antmicro/ddr5-tester/assets/previews/layer0.webp

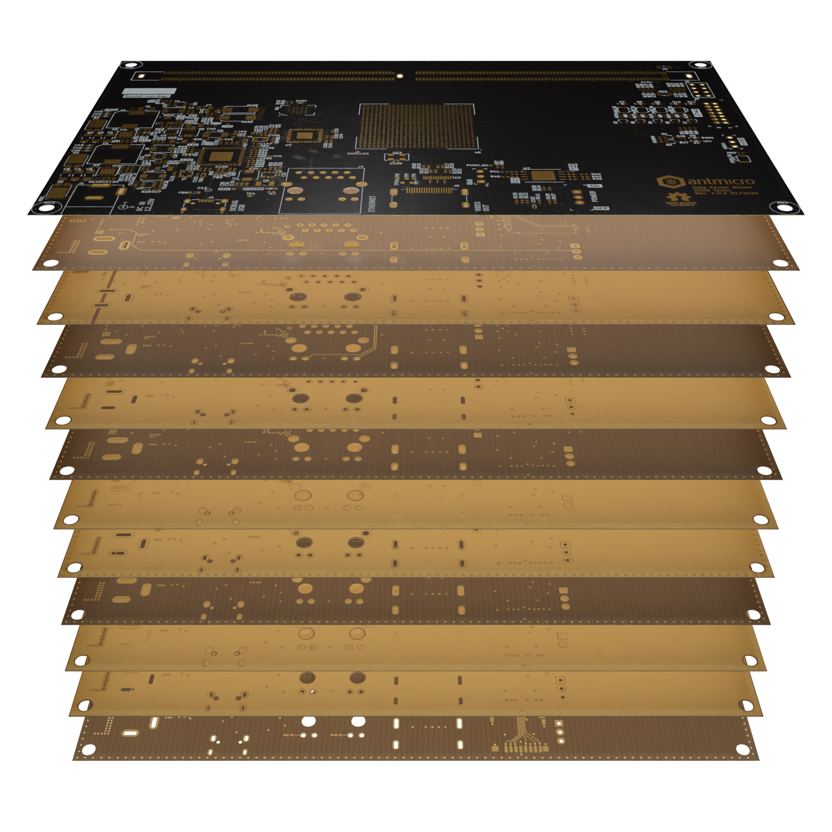
assets/previews/layer0.webp
