antmicro/ddr5-tester/assets/previews/layer2.png

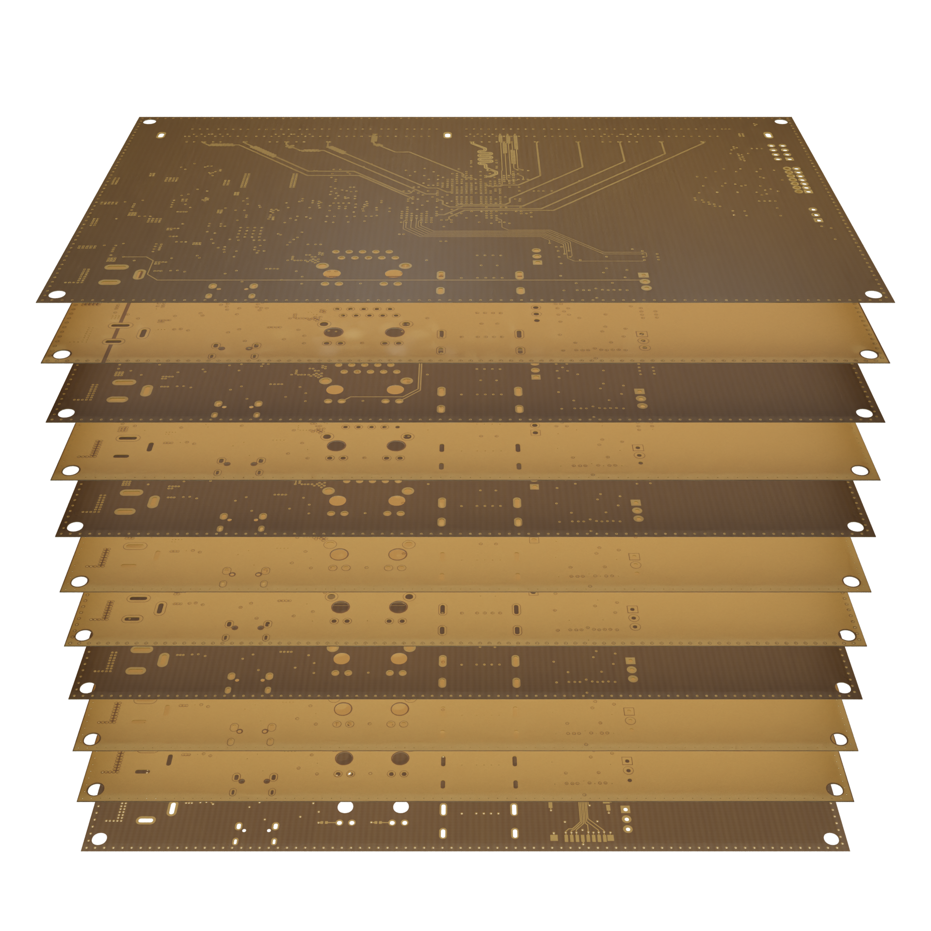
assets/previews/layer2.png
