antmicro/ddr5-tester/assets/previews/layer3.png

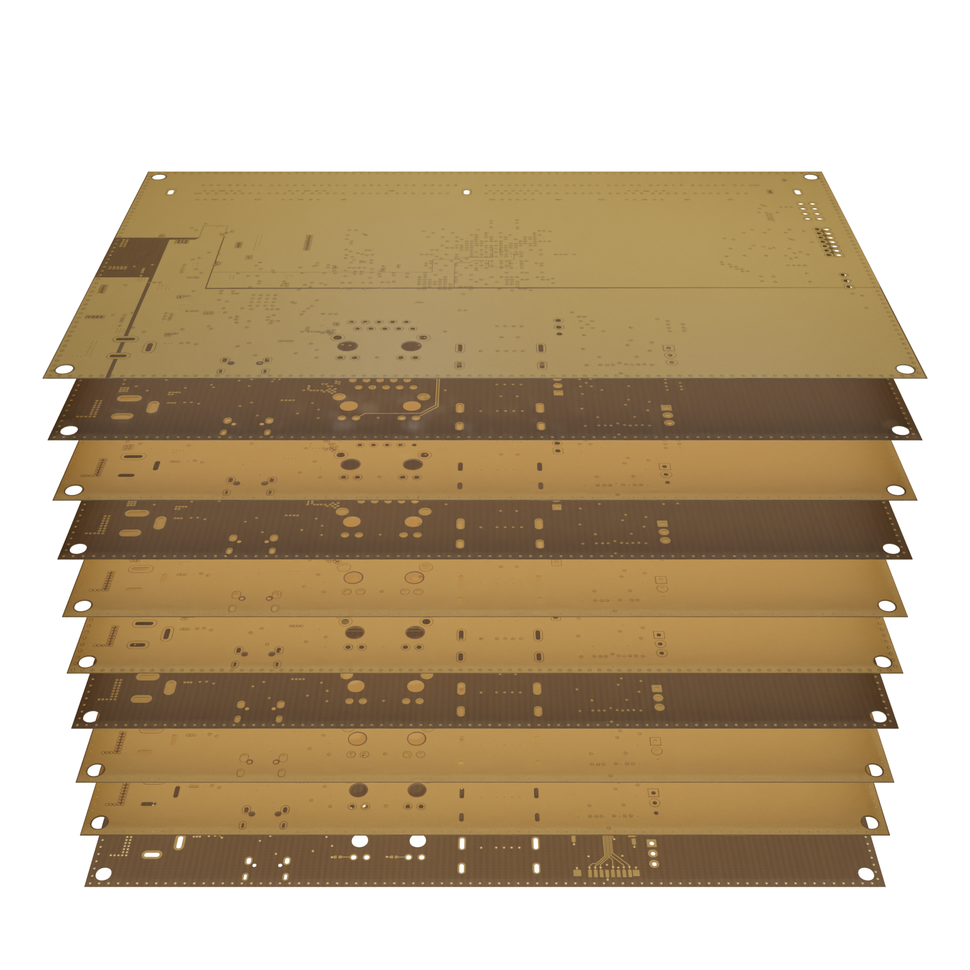
assets/previews/layer3.png
