antmicro/ddr5-tester/assets/previews/layer4.png

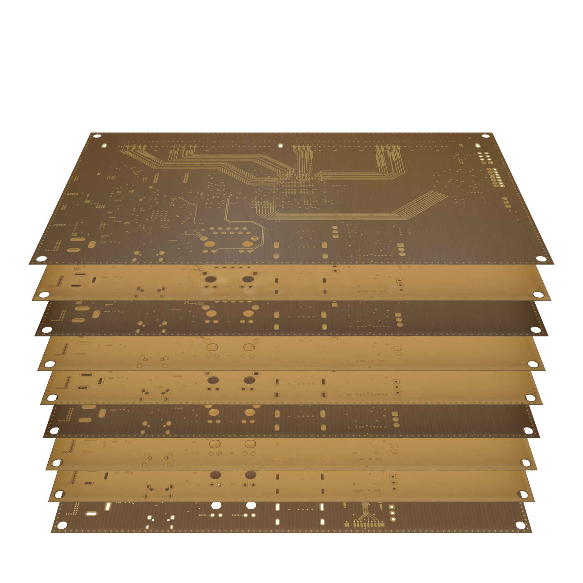
assets/previews/layer4.png
