antmicro/ddr5-tester/assets/previews/layer5.png

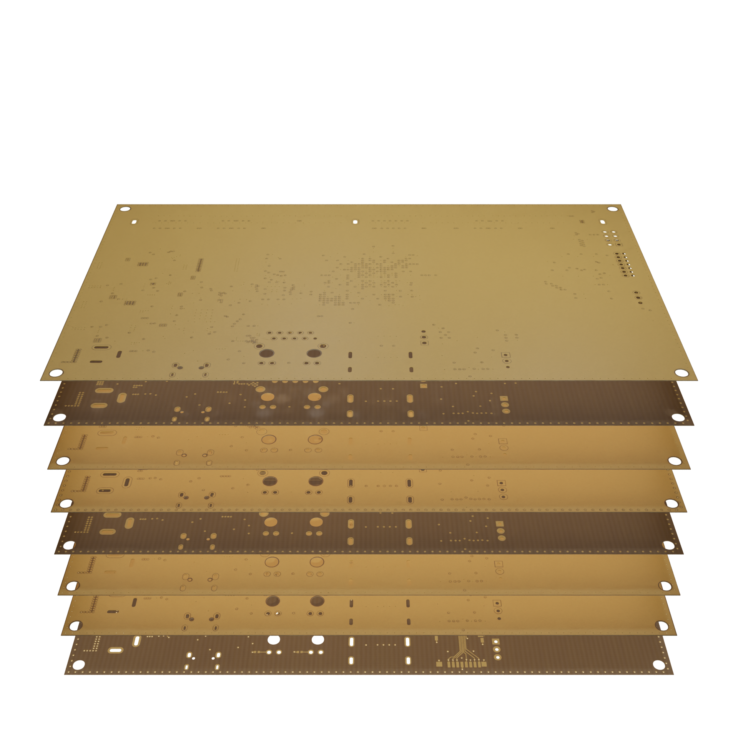
assets/previews/layer5.png
