antmicro/ddr5-tester/assets/previews/layer7.png

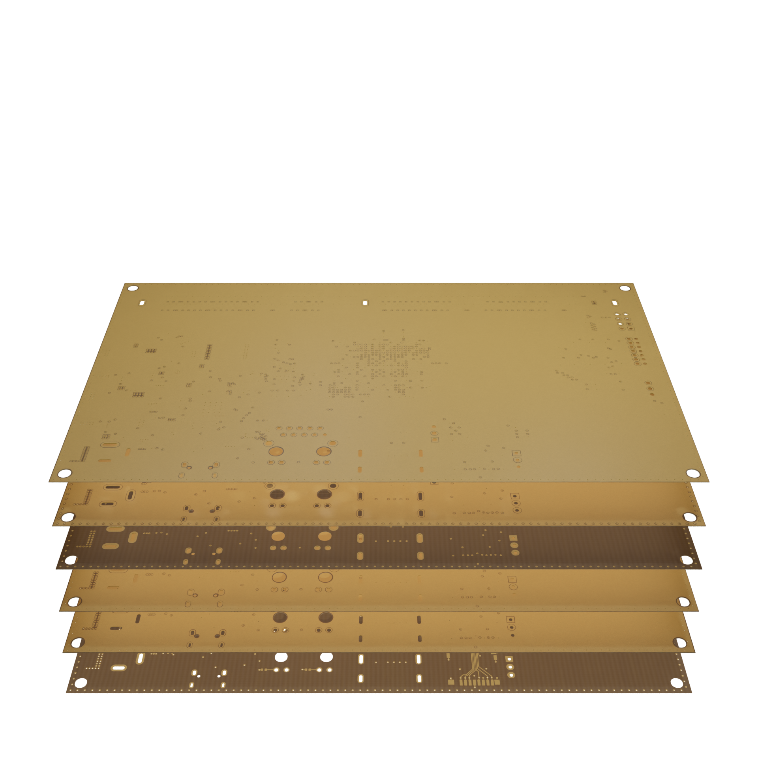
assets/previews/layer7.png
