antmicro/ddr5-tester/assets/previews/layer7_thumbnail.png

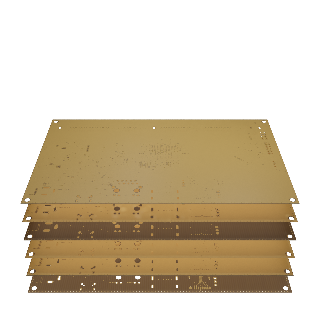
assets/previews/layer7_thumbnail.png
