antmicro/ddr5-tester/assets/previews/layer8.png

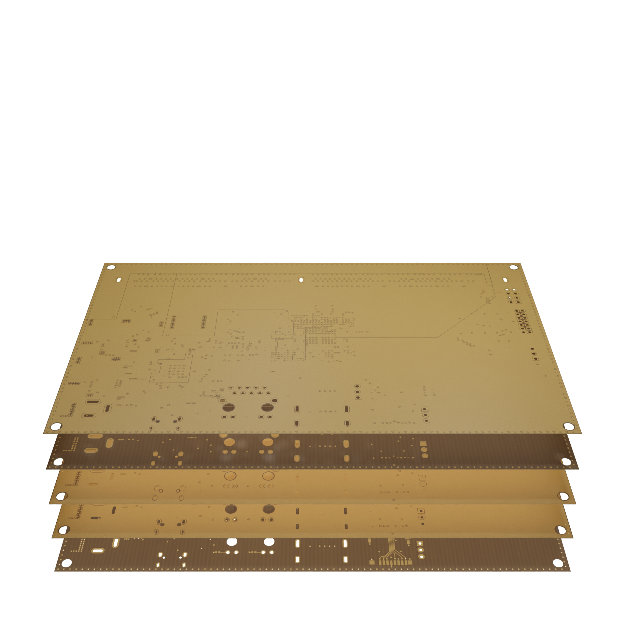
assets/previews/layer8.png
