antmicro/ddr5-tester/assets/previews/layer9.png

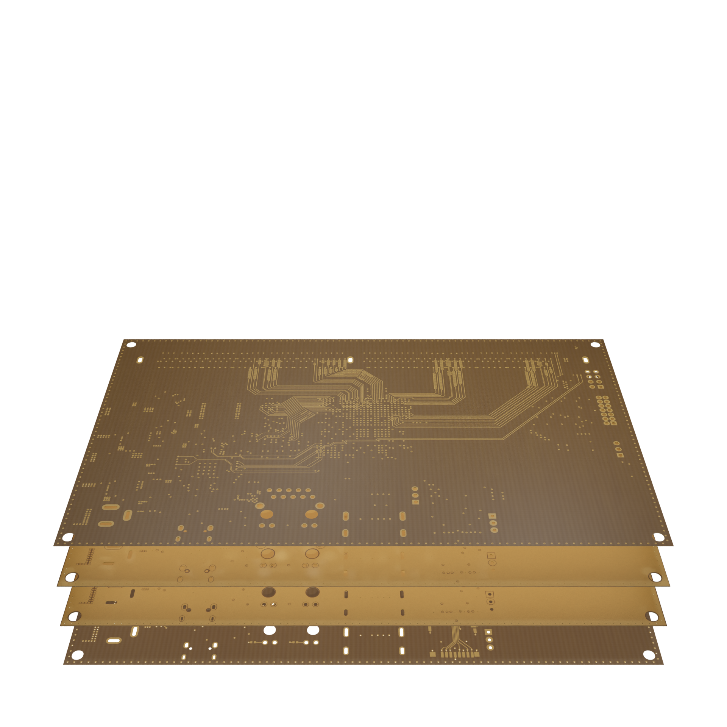
assets/previews/layer9.png
