antmicro/ddr5-tester/assets/previews/layer10.png

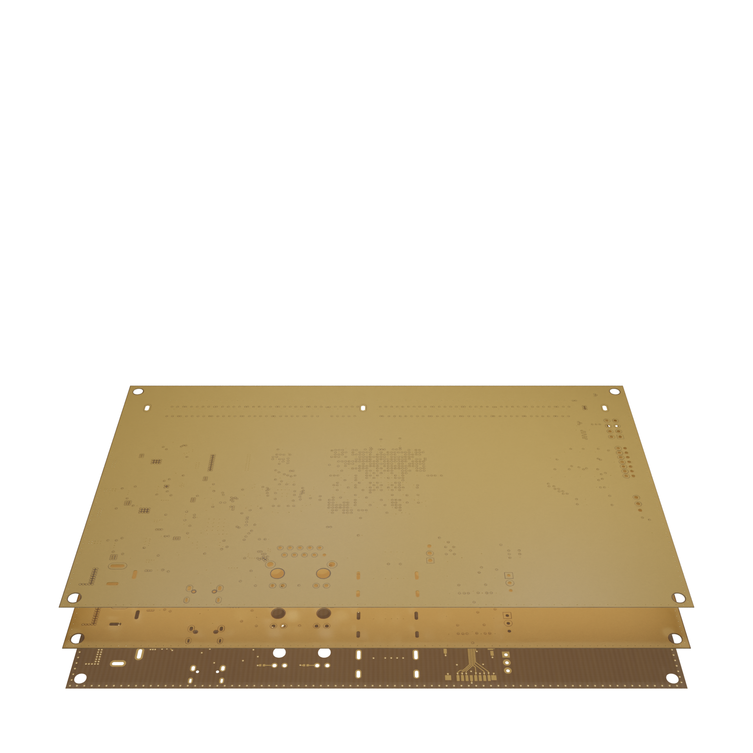
assets/previews/layer10.png
