antmicro/ddr5-tester/assets/previews/layer10_thumbnail.png

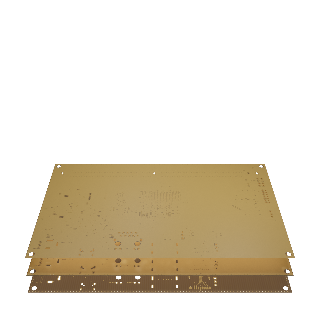
assets/previews/layer10_thumbnail.png
