antmicro/ddr5-tester/assets/previews/layer11.png

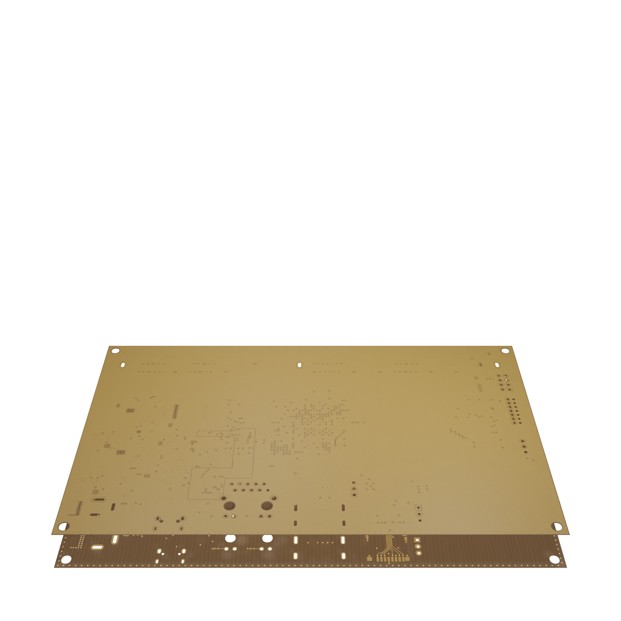
assets/previews/layer11.png
