antmicro/ddr5-tester/assets/previews/layer12.png

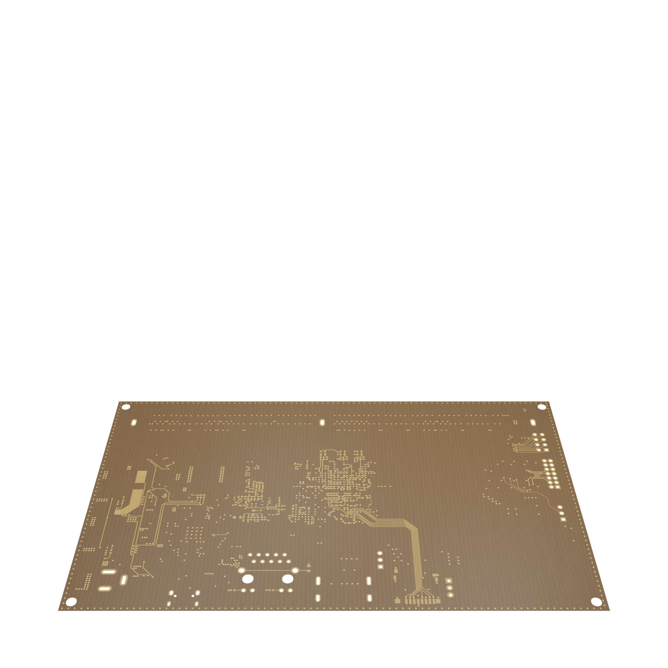
assets/previews/layer12.png
