antmicro/ddr5-tester/assets/previews/leftB.png

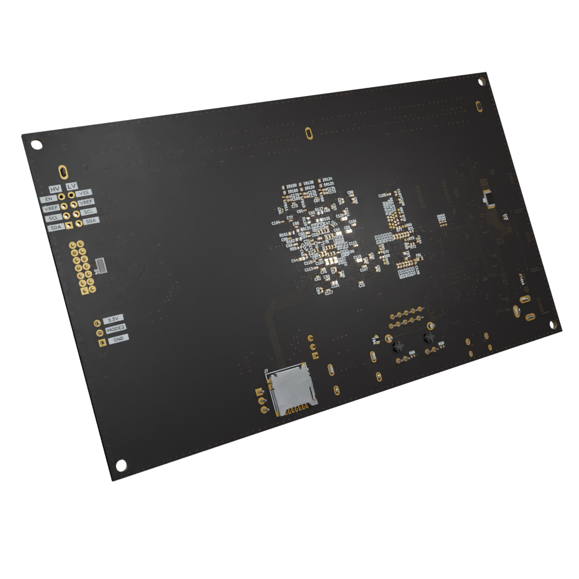
assets/previews/leftB.png
