antmicro/ddr5-tester/assets/previews/leftT.png

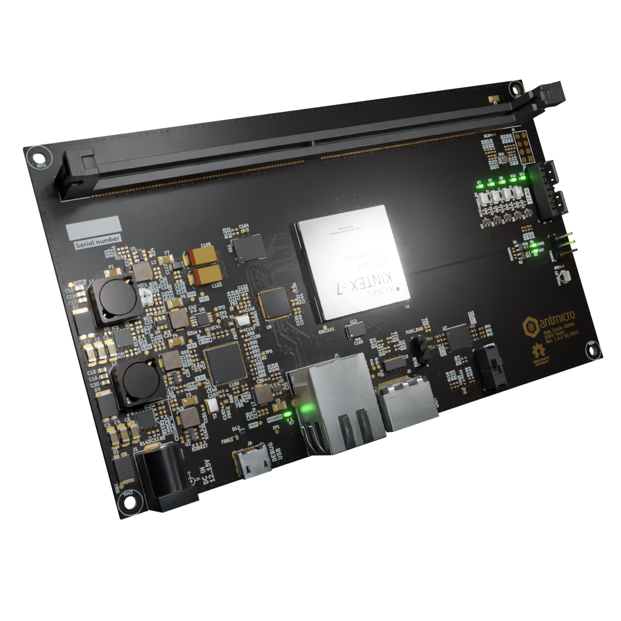
assets/previews/leftT.png
