antmicro/ddr5-tester/assets/previews/orthoB.png

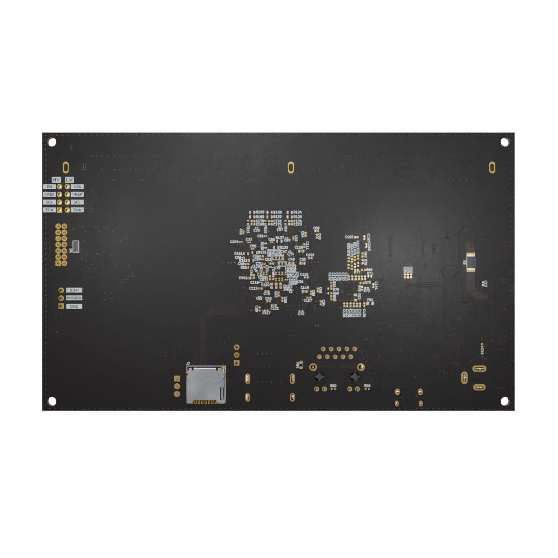
assets/previews/orthoB.png
