antmicro/ddr5-tester/assets/previews/orthoT.png

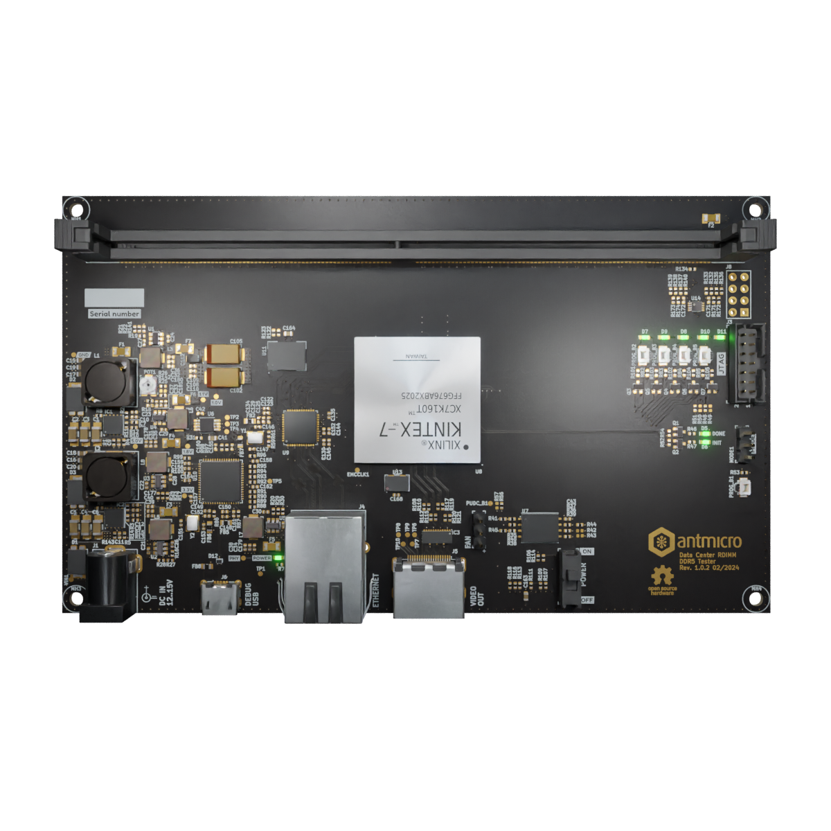
assets/previews/orthoT.png
