antmicro/ddr5-tester/assets/previews/photoB.png

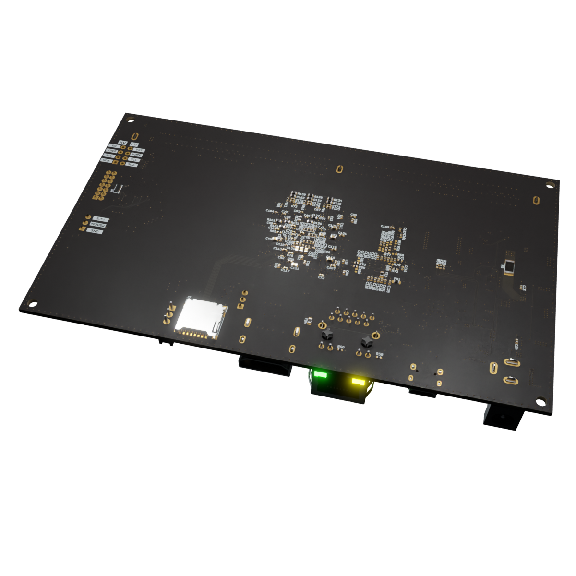
assets/previews/photoB.png
