antmicro/ddr5-tester/assets/previews/photoT.png

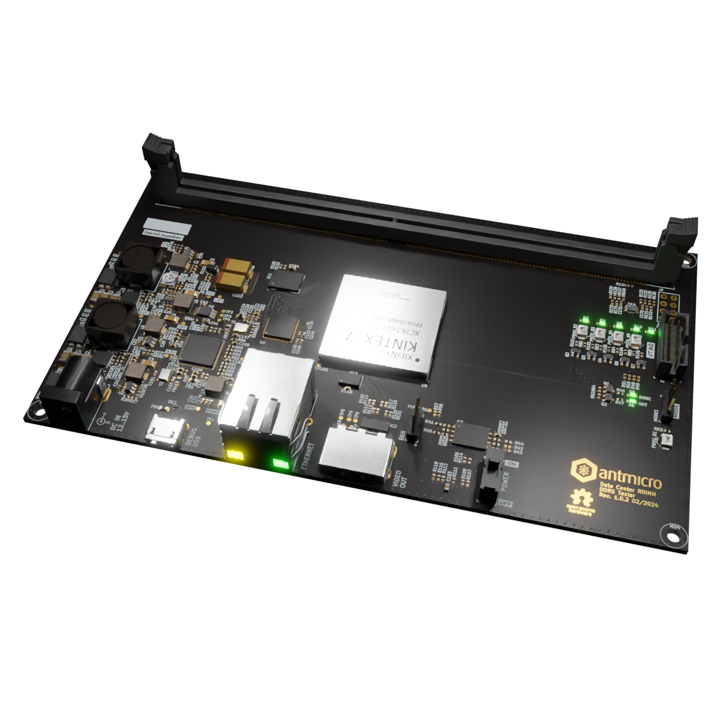
assets/previews/photoT.png
