antmicro/ddr5-tester/assets/previews/rightB.png

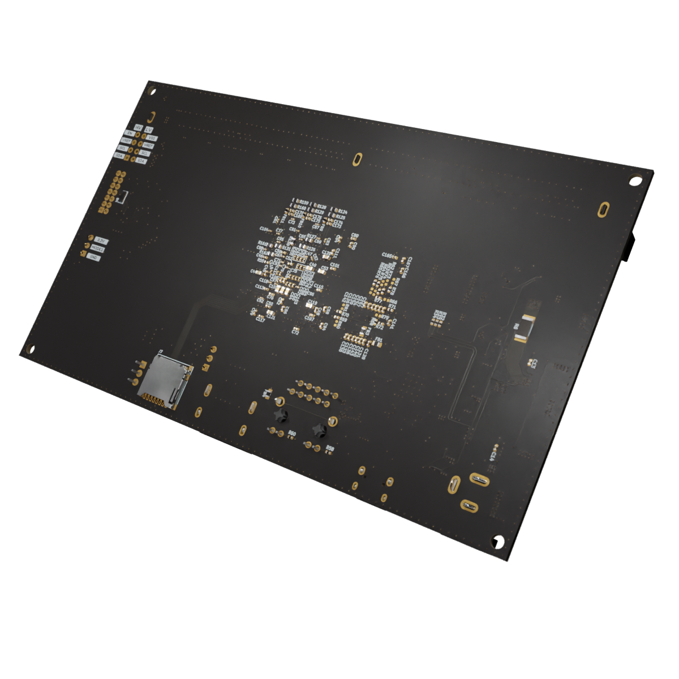
assets/previews/rightB.png
