antmicro/ddr5-tester/assets/previews/rightT.png

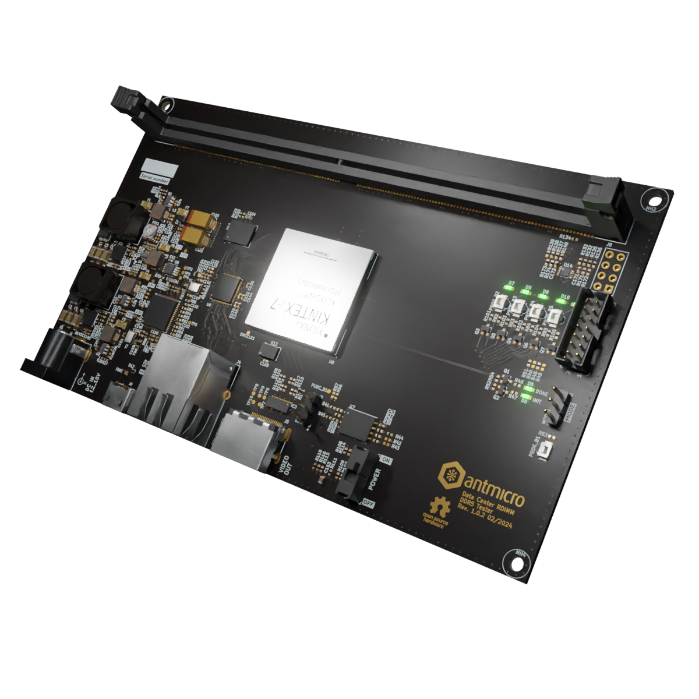
assets/previews/rightT.png
