antmicro/ddr5-tester/DDR5.kicad_sch

## KiCad design DDR5.kicad_sch (2024-02-20)

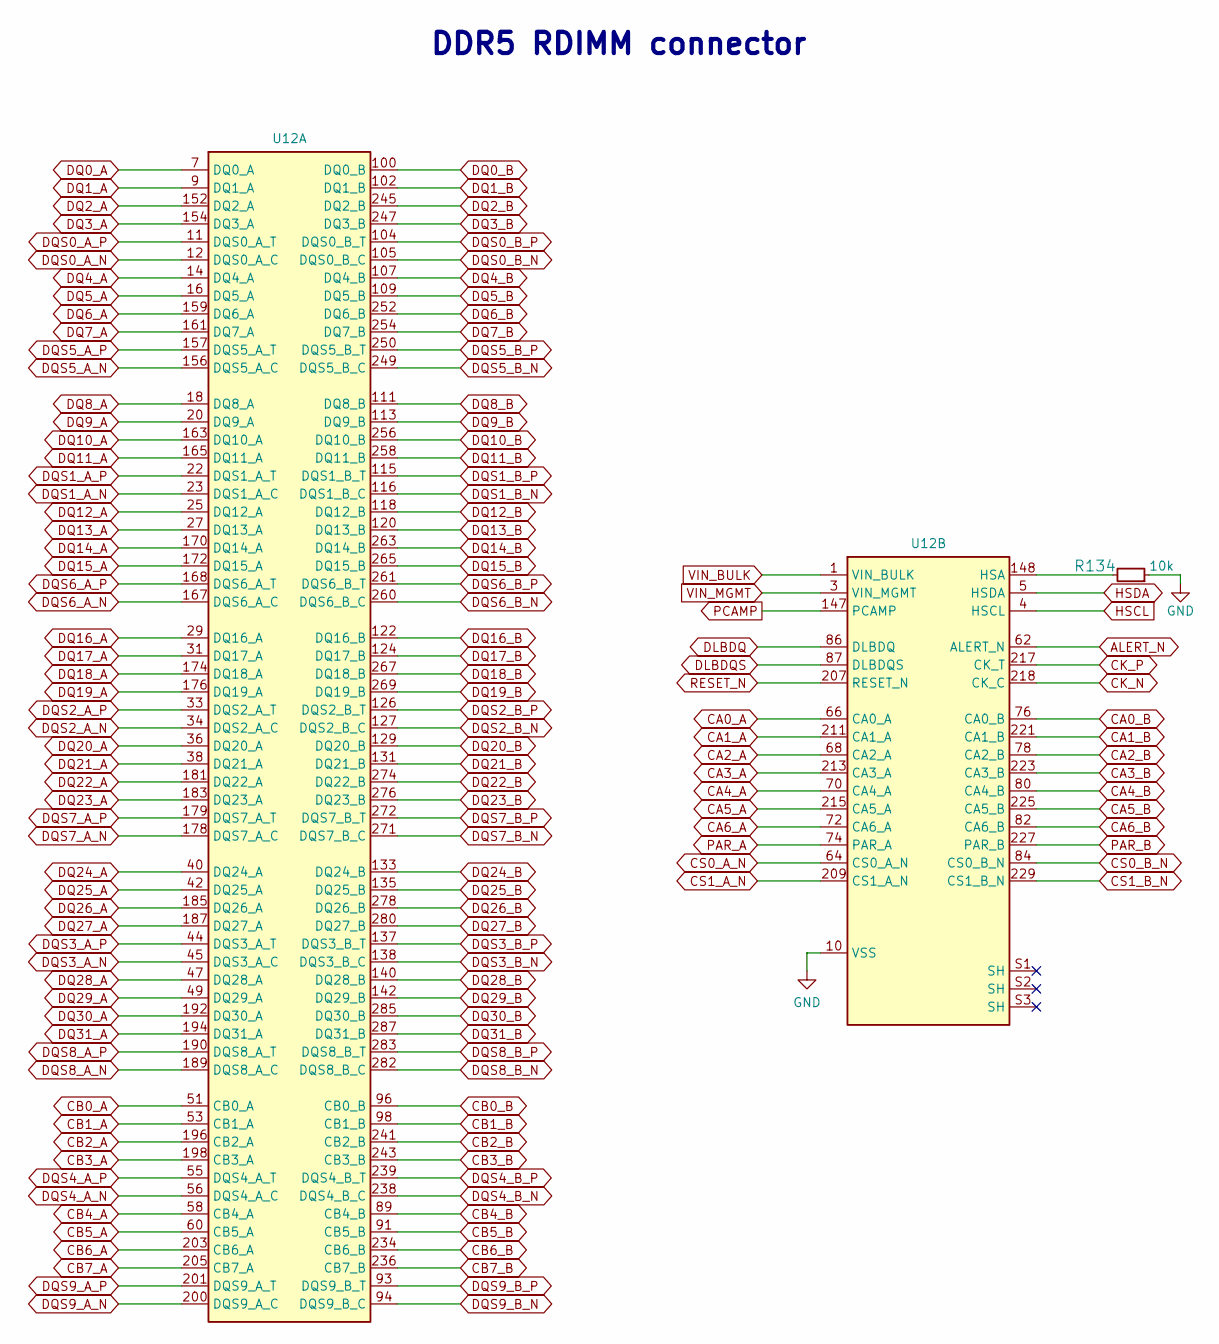
[picture p35: schematic DDR5.kicad_sch]

Parts:
R134: R_10k_0402; R_0402_1005Metric; Tolerance 1%; MPN CR0402-FX-1002GLF
U12: Bus_DDR5_DDR504111002KQ; Bus_DDR5_Socket_Amphenol_DDR504111002KQ; MPN DDR504111002KQ

Connections:
ALERT_N: U12.62 (ALERT_N)
CA0_A: U12.66 (CA0_A)
CA0_B: U12.76 (CA0_B)
CA1_A: U12.211 (CA1_A)
CA1_B: U12.221 (CA1_B)
CA2_A: U12.68 (CA2_A)
CA2_B: U12.78 (CA2_B)
CA3_A: U12.213 (CA3_A)
CA3_B: U12.223 (CA3_B)
CA4_A: U12.70 (CA4_A)
CA4_B: U12.80 (CA4_B)
CA5_A: U12.215 (CA5_A)
CA5_B: U12.225 (CA5_B)
CA6_A: U12.72 (CA6_A)
CA6_B: U12.82 (CA6_B)
CB0_A: U12.51 (CB0_A)
CB0_B: U12.96 (CB0_B)
CB1_A: U12.53 (CB1_A)
CB1_B: U12.98 (CB1_B)
CB2_A: U12.196 (CB2_A)
CB2_B: U12.241 (CB2_B)
CB3_A: U12.198 (CB3_A)
CB3_B: U12.243 (CB3_B)
CB4_A: U12.58 (CB4_A)
CB4_B: U12.89 (CB4_B)
CB5_A: U12.60 (CB5_A)
CB5_B: U12.91 (CB5_B)
CB6_A: U12.203 (CB6_A)
CB6_B: U12.234 (CB6_B)
CB7_A: U12.205 (CB7_A)
CB7_B: U12.236 (CB7_B)
CK_N: U12.218 (CK_C)
CK_P: U12.217 (CK_T)
CS0_A_N: U12.64 (CS0_A_N)
CS0_B_N: U12.84 (CS0_B_N)
CS1_A_N: U12.209 (CS1_A_N)
CS1_B_N: U12.229 (CS1_B_N)
DLBDQ: U12.86 (DLBDQ)
DLBDQS: U12.87 (DLBDQS)
DQ0_A: U12.7 (DQ0_A)
DQ0_B: U12.100 (DQ0_B)
DQ1_A: U12.9 (DQ1_A)
DQ1_B: U12.102 (DQ1_B)
DQ2_A: U12.152 (DQ2_A)
DQ2_B: U12.245 (DQ2_B)
DQ3_A: U12.154 (DQ3_A)
DQ3_B: U12.247 (DQ3_B)
DQ4_A: U12.14 (DQ4_A)
DQ4_B: U12.107 (DQ4_B)
DQ5_A: U12.16 (DQ5_A)
DQ5_B: U12.109 (DQ5_B)
DQ6_A: U12.159 (DQ6_A)
DQ6_B: U12.252 (DQ6_B)
DQ7_A: U12.161 (DQ7_A)
DQ7_B: U12.254 (DQ7_B)
DQ8_A: U12.18 (DQ8_A)
DQ8_B: U12.111 (DQ8_B)
DQ9_A: U12.20 (DQ9_A)
DQ9_B: U12.113 (DQ9_B)
DQ10_A: U12.163 (DQ10_A)
DQ10_B: U12.256 (DQ10_B)
DQ11_A: U12.165 (DQ11_A)
DQ11_B: U12.258 (DQ11_B)
DQ12_A: U12.25 (DQ12_A)
DQ12_B: U12.118 (DQ12_B)
DQ13_A: U12.27 (DQ13_A)
DQ13_B: U12.120 (DQ13_B)
DQ14_A: U12.170 (DQ14_A)
DQ14_B: U12.263 (DQ14_B)
DQ15_A: U12.172 (DQ15_A)
DQ15_B: U12.265 (DQ15_B)
DQ16_A: U12.29 (DQ16_A)
DQ16_B: U12.122 (DQ16_B)
DQ17_A: U12.31 (DQ17_A)
DQ17_B: U12.124 (DQ17_B)
DQ18_A: U12.174 (DQ18_A)
DQ18_B: U12.267 (DQ18_B)
DQ19_A: U12.176 (DQ19_A)
DQ19_B: U12.269 (DQ19_B)
DQ20_A: U12.36 (DQ20_A)
DQ20_B: U12.129 (DQ20_B)
DQ21_A: U12.38 (DQ21_A)
DQ21_B: U12.131 (DQ21_B)
DQ22_A: U12.181 (DQ22_A)
DQ22_B: U12.274 (DQ22_B)
DQ23_A: U12.183 (DQ23_A)
DQ23_B: U12.276 (DQ23_B)
DQ24_A: U12.40 (DQ24_A)
DQ24_B: U12.133 (DQ24_B)
DQ25_A: U12.42 (DQ25_A)
DQ25_B: U12.135 (DQ25_B)
DQ26_A: U12.185 (DQ26_A)
DQ26_B: U12.278 (DQ26_B)
DQ27_A: U12.187 (DQ27_A)
DQ27_B: U12.280 (DQ27_B)
DQ28_A: U12.47 (DQ28_A)
DQ28_B: U12.140 (DQ28_B)
DQ29_A: U12.49 (DQ29_A)
DQ29_B: U12.142 (DQ29_B)
DQ30_A: U12.192 (DQ30_A)
DQ30_B: U12.285 (DQ30_B)
DQ31_A: U12.194 (DQ31_A)
DQ31_B: U12.287 (DQ31_B)
DQS0_A_N: U12.12 (DQS0_A_C)
DQS0_A_P: U12.11 (DQS0_A_T)
DQS0_B_N: U12.105 (DQS0_B_C)
DQS0_B_P: U12.104 (DQS0_B_T)
DQS1_A_N: U12.23 (DQS1_A_C)
DQS1_A_P: U12.22 (DQS1_A_T)
DQS1_B_N: U12.116 (DQS1_B_C)
DQS1_B_P: U12.115 (DQS1_B_T)
DQS2_A_N: U12.34 (DQS2_A_C)
DQS2_A_P: U12.33 (DQS2_A_T)
DQS2_B_N: U12.127 (DQS2_B_C)
DQS2_B_P: U12.126 (DQS2_B_T)
DQS3_A_N: U12.45 (DQS3_A_C)
DQS3_A_P: U12.44 (DQS3_A_T)
DQS3_B_N: U12.138 (DQS3_B_C)
DQS3_B_P: U12.137 (DQS3_B_T)
DQS4_A_N: U12.56 (DQS4_A_C)
DQS4_A_P: U12.55 (DQS4_A_T)
DQS4_B_N: U12.238 (DQS4_B_C)
DQS4_B_P: U12.239 (DQS4_B_T)
DQS5_A_N: U12.156 (DQS5_A_C)
DQS5_A_P: U12.157 (DQS5_A_T)
DQS5_B_N: U12.249 (DQS5_B_C)
DQS5_B_P: U12.250 (DQS5_B_T)
DQS6_A_N: U12.167 (DQS6_A_C)
DQS6_A_P: U12.168 (DQS6_A_T)
DQS6_B_N: U12.260 (DQS6_B_C)
DQS6_B_P: U12.261 (DQS6_B_T)
DQS7_A_N: U12.178 (DQS7_A_C)
DQS7_A_P: U12.179 (DQS7_A_T)
DQS7_B_N: U12.271 (DQS7_B_C)
DQS7_B_P: U12.272 (DQS7_B_T)
DQS8_A_N: U12.189 (DQS8_A_C)
DQS8_A_P: U12.190 (DQS8_A_T)
DQS8_B_N: U12.282 (DQS8_B_C)
DQS8_B_P: U12.283 (DQS8_B_T)
DQS9_A_N: U12.200 (DQS9_A_C)
DQS9_A_P: U12.201 (DQS9_A_T)
DQS9_B_N: U12.94 (DQS9_B_C)
DQS9_B_P: U12.93 (DQS9_B_T)
GND: R134.1, U12.6 (VSS), U12.8 (VSS), U12.10 (VSS), U12.13 (VSS), U12.15 (VSS), U12.17 (VSS), U12.19 (VSS), U12.21 (VSS), U12.24 (VSS), U12.26 (VSS), U12.28 (VSS), U12.30 (VSS), U12.32 (VSS), U12.35 (VSS), U12.37 (VSS), U12.39 (VSS), U12.41 (VSS), U12.43 (VSS), U12.46 (VSS), U12.48 (VSS), U12.50 (VSS), U12.52 (VSS), U12.54 (VSS), U12.57 (VSS), U12.59 (VSS), U12.61 (VSS), U12.63 (VSS), U12.65 (VSS), U12.67 (VSS), U12.69 (VSS), U12.71 (VSS), U12.73 (VSS), U12.75 (VSS), U12.77 (VSS), U12.79 (VSS), U12.81 (VSS), U12.83 (VSS), U12.85 (VSS), U12.88 (VSS), U12.90 (VSS), U12.92 (VSS), U12.95 (VSS), U12.97 (VSS), U12.99 (VSS), U12.101 (VSS), U12.103 (VSS), U12.106 (VSS), U12.108 (VSS), U12.110 (VSS), U12.112 (VSS), U12.114 (VSS), U12.117 (VSS), U12.119 (VSS), U12.121 (VSS), U12.123 (VSS), U12.125 (VSS), U12.128 (VSS), U12.130 (VSS), U12.132 (VSS), U12.134 (VSS), U12.136 (VSS), U12.139 (VSS), U12.141 (VSS), U12.143 (VSS), U12.151 (VSS), U12.153 (VSS), U12.155 (VSS), U12.158 (VSS), U12.160 (VSS), U12.162 (VSS), U12.164 (VSS), U12.166 (VSS), U12.169 (VSS), U12.171 (VSS), U12.173 (VSS), U12.175 (VSS), U12.177 (VSS), U12.180 (VSS), U12.182 (VSS), U12.184 (VSS), U12.186 (VSS), U12.188 (VSS), U12.191 (VSS), U12.193 (VSS), U12.195 (VSS), U12.197 (VSS), U12.199 (VSS), U12.202 (VSS), U12.204 (VSS), U12.206 (VSS), U12.208 (VSS), U12.210 (VSS), U12.212 (VSS), U12.214 (VSS), U12.216 (VSS), U12.219 (VSS), U12.222 (VSS), U12.224 (VSS), U12.226 (VSS), U12.228 (VSS), U12.230 (VSS), U12.233 (VSS), U12.235 (VSS), U12.237 (VSS), U12.240 (VSS), U12.242 (VSS), U12.244 (VSS), U12.246 (VSS), U12.248 (VSS), U12.251 (VSS), U12.253 (VSS), U12.255 (VSS), U12.257 (VSS), U12.259 (VSS), U12.262 (VSS), U12.264 (VSS), U12.266 (VSS), U12.268 (VSS), U12.270 (VSS), U12.273 (VSS), U12.275 (VSS), U12.277 (VSS), U12.279 (VSS), U12.281 (VSS), U12.284 (VSS), U12.286 (VSS), U12.288 (VSS)
HSCL: U12.4 (HSCL)
HSDA: U12.5 (HSDA)
unnamed: R134.2, U12.148 (HSA)
PAR_A: U12.74 (PAR_A)
PAR_B: U12.227 (PAR_B)
PCAMP: U12.147 (PCAMP)
RESET_N: U12.207 (RESET_N)
VIN_BULK: U12.1 (VIN_BULK), U12.145 (VIN_BULK), U12.146 (VIN_BULK)
VIN_MGMT: U12.3 (VIN_MGMT)

Notes on the sheet:
DDR5 RDIMM connector
