antmicro/ddr5-tester/config-spi.kicad_sch

## KiCad design config-spi.kicad_sch (2024-02-20)

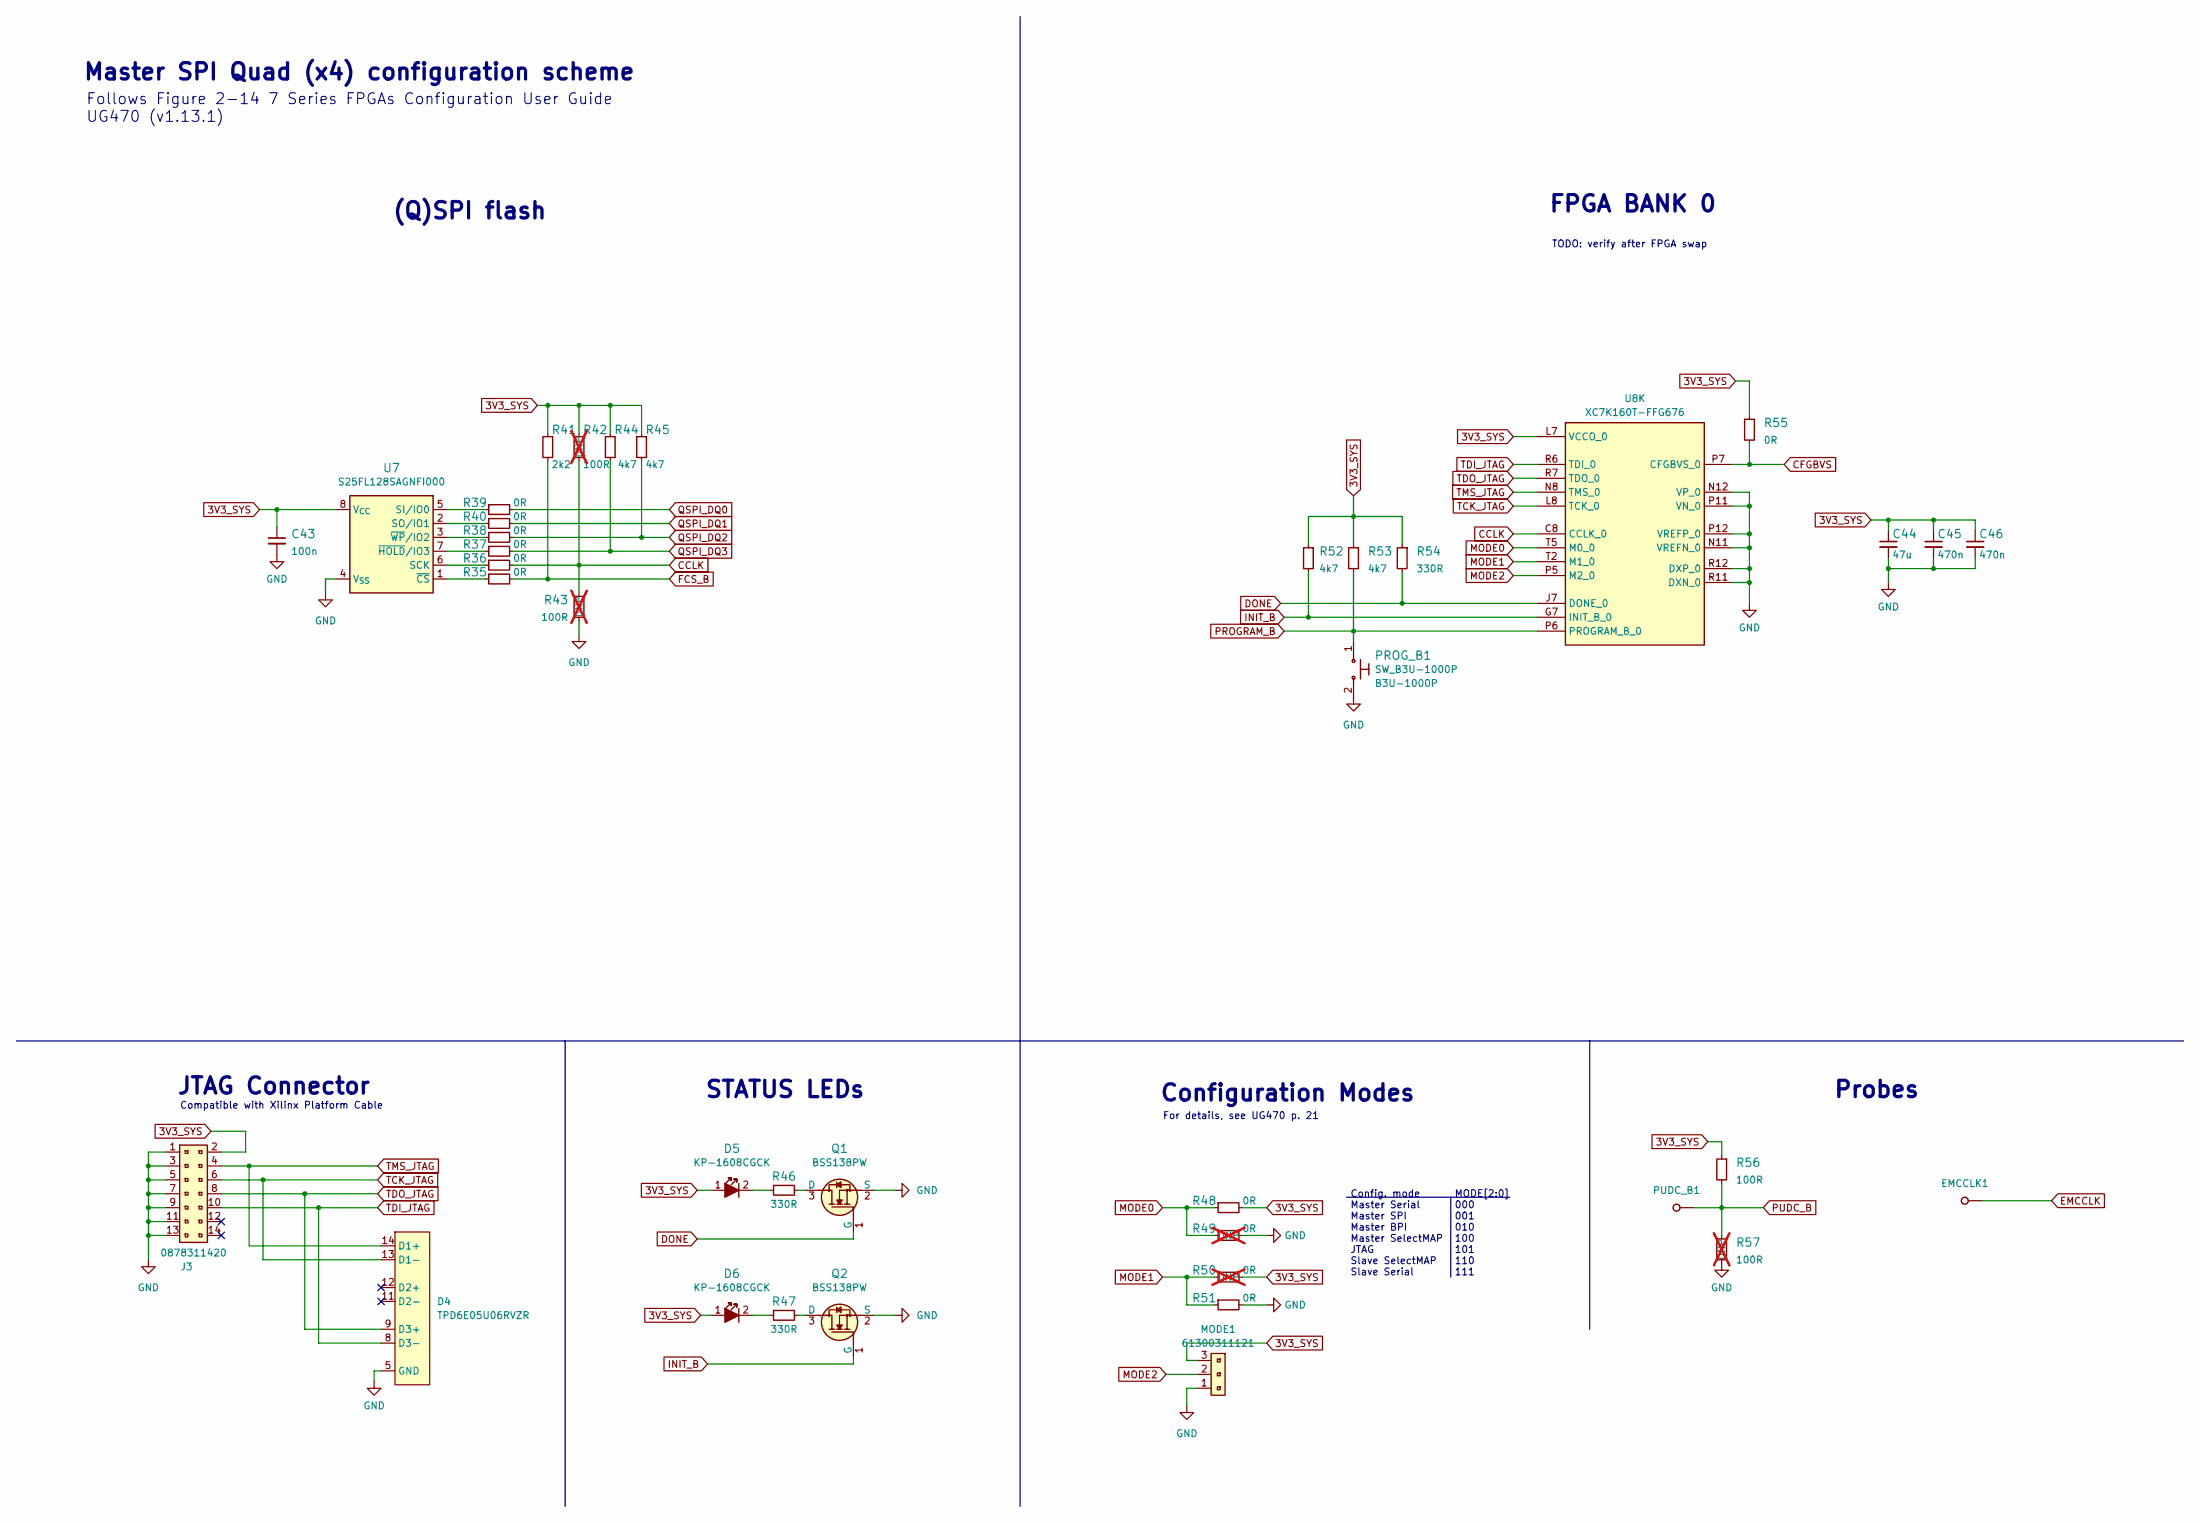
[picture p36: schematic config-spi.kicad_sch]

Parts:
C43: C_100n_6V3_0402; C_0402_1005Metric; MPN 0402X104K6R3CT
C44: C_47u_0603; C_0603_1608Metric; MPN GRM188R60J476ME15D
C45, C46: C_470n_0402; C_0402_1005Metric; MPN C1005X5R1E474M050BB
D4: TPD6E05U06RVZR; USON-14_3.5X1.3X0.5mm_P0.5mm; MPN TPD6E05U06RVZR
D5, D6: LED_G_0603_KP-1608CGCK; LED_0603_1608Metric_G; MPN KP-1608CGCK
EMCCLK1: TP_1mm_SMD; TP_SMD_1mm
J3: PinHeader_2x7_P2mm_Drill1mm_Shrouded; MPN 0878311420
MODE1: PinHeader_1x3_P2.54mm_Drill1.1mm; MPN 61300311121
PROG_B1: SW_B3U-1000P; SW_B3U-1000P_SMD; MPN B3U-1000P
PUDC_B1: TP_1mm_SMD; TP_SMD_1mm
Q1, Q2: BSS138PW; SC70-3; MPN BSS138PW
R35, R36, R37, R38, R39, R40, R48, R51, R55: R_0R_0402; R_0402_1005Metric; MPN ERJ2GE0R00X
R41: R_2k2_0402; R_0402_1005Metric; Tolerance 1%; MPN CR0402-FX-2201GLF
R42, R43, R57: R_100R_0402; R_0402_1005Metric; Tolerance 1%; MPN CR0402-FX-1000GLF; not fitted
R44, R45, R52, R53: R_4k7_0402; R_0402_1005Metric; Tolerance 1%; MPN CR0402-FX-4701GLF
R46, R47, R54: R_330R_0402; R_0402_1005Metric; Tolerance 1%; MPN CR0402-FX-3300GLF
R49, R50: R_0R_0402; R_0402_1005Metric; MPN ERJ2GE0R00X; not fitted
R56: R_100R_0402; R_0402_1005Metric; Tolerance 1%; MPN CR0402-FX-1000GLF
U7: S25FL128SAGNFI000; WSON-8_6x8x0.5mm_P1.27mm; MPN S25FL128SAGNFI000
U8: XC7K160T-FFG676; BGA-676_27x27mm_Layout26x26_P1X1mm; MPN XC7K160T-FFG676

Connections:
3V3_SYS: C43.1, C44.1, C45.1, C46.1, D5.1, D6.1, J3.2, MODE1.3, R41.1, R42.1, R44.1, R45.1, R48.2, R50.2, R52.1, R53.1, R54.1, R55.1, R56.1, U7.8 (V_{CC}), U8.L7 (VCCO_0), U8.T6 (VCCO_0)
CCLK: R36.2, R42.2, R43.1, U8.C8 (CCLK_0)
CFGBVS: R55.2, U8.P7 (CFGBVS_0)
DONE: Q1.1 (G), R54.2, U8.J7 (DONE_0)
EMCCLK: EMCCLK1.1
FCS_B: R35.2, R41.2
GND: C43.2, C44.2, C45.2, C46.2, D4.5 (GND), D4.10 (GND), J3.1, J3.3, J3.5, J3.7, J3.9, J3.11, J3.13, MODE1.1, PROG_B1.2, Q1.2 (S), Q2.2 (S), R43.2, R49.2, R51.2, R57.2, U7.4 (V_{SS}), U8.N11 (VREFN_0), U8.N12 (VP_0), U8.P11 (VN_0), U8.P12 (VREFP_0), U8.R11 (DXN_0), U8.R12 (DXP_0)
INIT_B: Q2.1 (G), R52.2, U8.G7 (INIT_B_0)
MODE0: R48.1, R49.1, U8.T5 (M0_0)
MODE1: R50.1, R51.1, U8.T2 (M1_0)
MODE2: MODE1.2, U8.P5 (M2_0)
unnamed: D4.4 (D2-), D4.11 (D2-)
unnamed: D4.3 (D2+), D4.12 (D2+)
unnamed: D5.2, R46.1
unnamed: D6.2, R47.1
unnamed: Q1.3 (D), R46.2
unnamed: Q2.3 (D), R47.2
unnamed: R35.1, U7.1 (~CS)
unnamed: R36.1, U7.6 (SCK)
unnamed: R37.1, U7.7 (~HOLD/IO3)
unnamed: R38.1, U7.3 (~WP/IO2)
unnamed: R39.1, U7.5 (SI/IO0)
unnamed: R40.1, U7.2 (SO/IO1)
PROGRAM_B: PROG_B1.1, R53.2, U8.P6 (PROGRAM_B_0)
PUDC_B: PUDC_B1.1, R56.2, R57.1
QSPI_DQ0: R39.2
QSPI_DQ1: R40.2
QSPI_DQ2: R38.2, R45.2
QSPI_DQ3: R37.2, R44.2
TCK_JTAG: D4.2 (D1-), D4.13 (D1-), J3.6, U8.L8 (TCK_0)
TDI_JTAG: D4.7 (D3-), D4.8 (D3-), J3.10, U8.R6 (TDI_0)
TDO_JTAG: D4.6 (D3+), D4.9 (D3+), J3.8, U8.R7 (TDO_0)
TMS_JTAG: D4.1 (D1+), D4.14 (D1+), J3.4, U8.N8 (TMS_0)

Notes on the sheet:
Master SPI Quad (x4) configuration scheme
JTAG Connector
Config. mode Master Serial Master SPI Master BPI Master SelectMAP JTAG Slave SelectMAP Slave Serial
(Q)SPI flash
STATUS LEDs
Configuration Modes
FPGA BANK 0
MODE[2:0] 000 001 010 100 101 110 111
TODO: verify after FPGA swap
Follows Figure 2-14 7 Series FPGAs Configuration User Guide UG470 (v1.13.1)
Compatible with Xilinx Platform Cable
For details, see UG470 p. 21
Probes
