antmicro/ddr5-tester/data-center-rdimm-ddr5-tester.kicad_sch

## KiCad design data-center-rdimm-ddr5-tester.kicad_sch (2024-02-20)

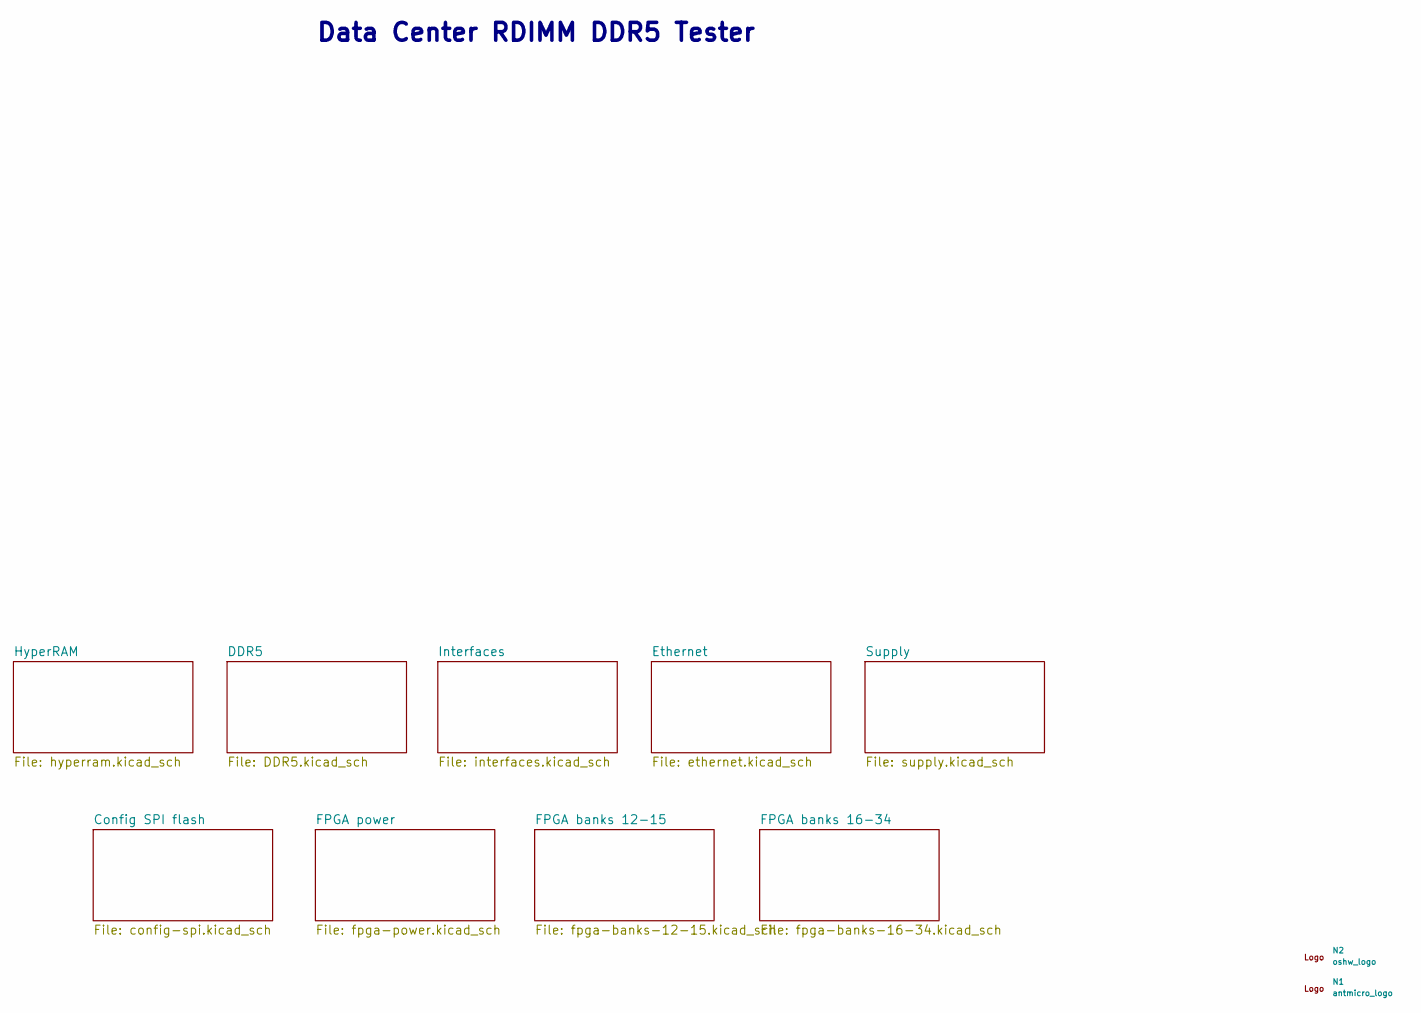
[picture p37: schematic data-center-rdimm-ddr5-tester.kicad_sch]

Parts:
N1: antmicro_logo; antmicro-logo
N2: oshw_logo; oshw-logo

Notes on the sheet:
Data Center RDIMM DDR5 Tester
