antmicro/ddr5-tester/ethernet.kicad_sch

## KiCad design ethernet.kicad_sch (2024-02-20)

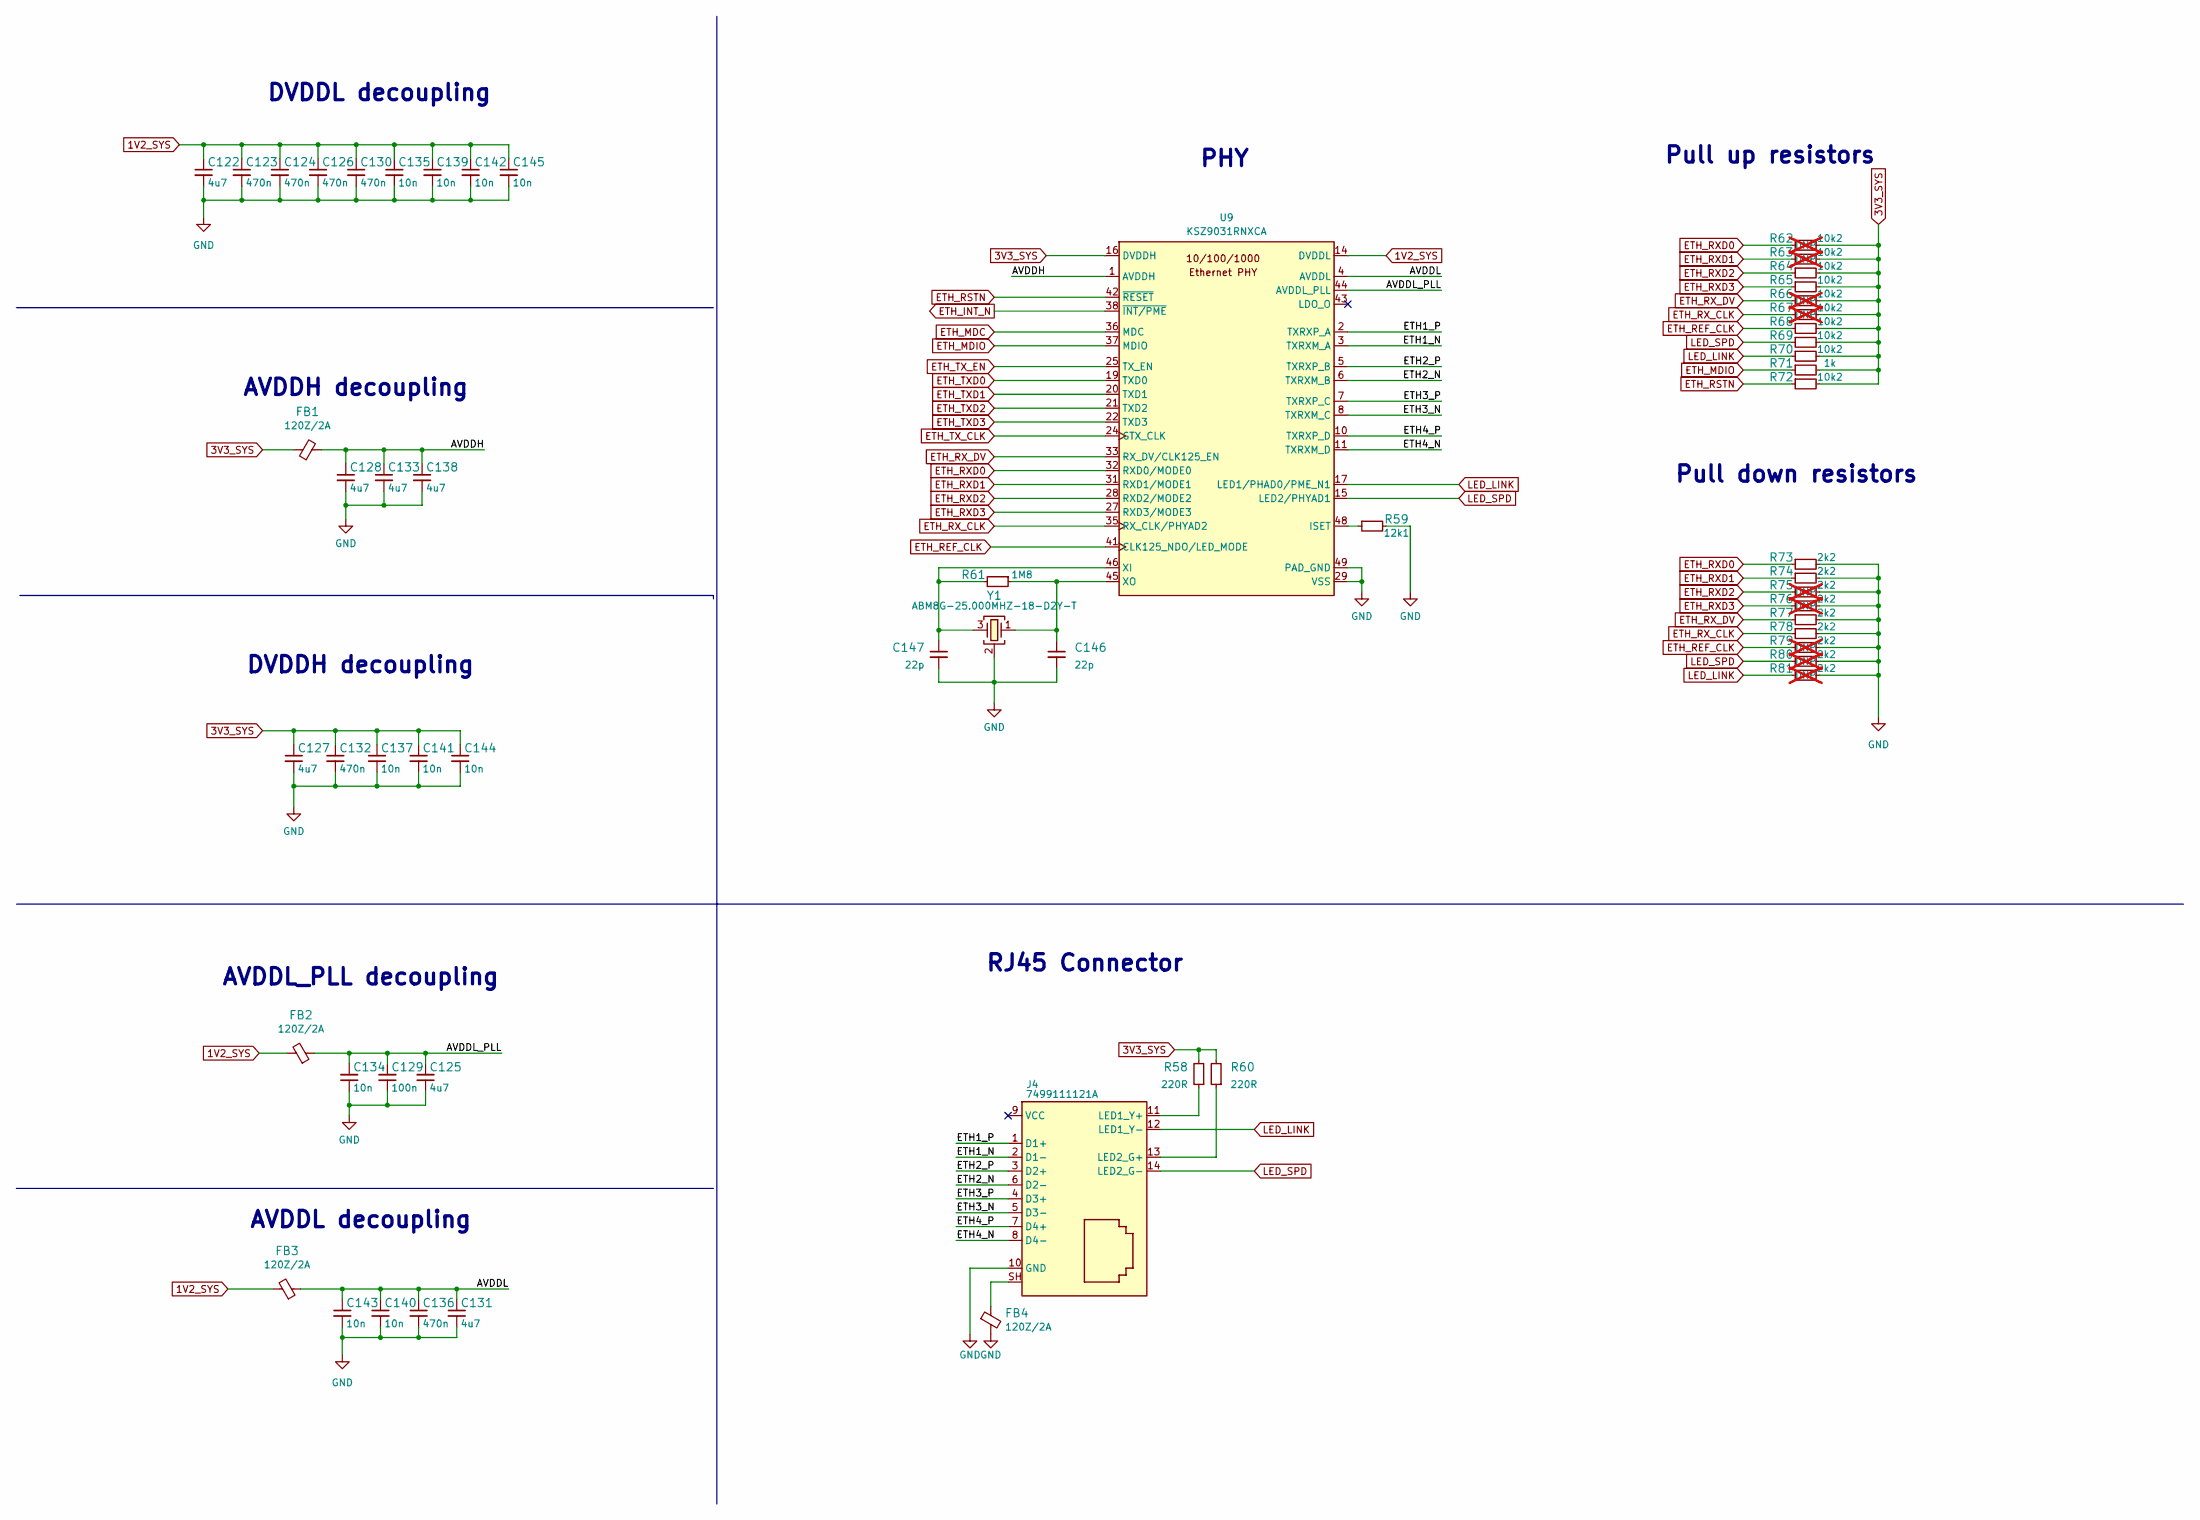
[picture p38: schematic ethernet.kicad_sch]

Parts:
C122, C125, C127, C128, C131, C133, C138: C_4u7_0402; C_0402_1005Metric; MPN GRM155R61A475MEAAD
C123, C124, C126, C130, C132, C136: C_470n_0402; C_0402_1005Metric; MPN C1005X5R1E474M050BB
C129: C_100n_16V_0402; C_0402_1005Metric; MPN MC0402B104K160CT
C134, C135, C137, C139, C140, C141, C142, C143, C144, C145: C_10n_0402; C_0402_1005Metric; Voltage 50V; MPN GRM155R71H103KA88D
C146, C147: C_22p_0402; C_0402_1005Metric; MPN CC0402JRNPO9BN220
FB1, FB2, FB3, FB4: FB_120Z_2A_0603; FB_0603_1608Metric; MPN BLM18PG121SN1D
J4: Bus_RJ45_7499111121A; RJ45_7499111121A_Horizontal; MPN 7499111121A
R58, R60: R_220R_0402; R_0402_1005Metric; Tolerance 1%; MPN CR0402-FX-2200GLF
R59: R_12k1_0402; R_0402_1005Metric; Tolerance 1%; MPN CR0402-FX-1212GLF
R61: R_1M8_0402; R_0402_1005Metric; Tolerance 1%; MPN CR0402-FX-1804GLF
R62, R63, R66, R67: R_10k2_0402; R_0402_1005Metric; Tolerance 1%; MPN CR0402-FX-1022GLF; not fitted
R64, R65, R68, R69, R70, R72: R_10k2_0402; R_0402_1005Metric; Tolerance 1%; MPN CR0402-FX-1022GLF
R71: R_1k_0402; R_0402_1005Metric; Tolerance 1%; MPN CR0402-FX-1001GLF
R73, R74, R77, R78: R_2k2_0402; R_0402_1005Metric; Tolerance 1%; MPN CR0402-FX-2201GLF
R75, R76, R79, R80, R81: R_2k2_0402; R_0402_1005Metric; Tolerance 1%; MPN CR0402-FX-2201GLF; not fitted
U9: KSZ9031RNXCA; QFN-48-1EP_7x7x0.9mm_P0.5mm_EP3.5x3.5mm; MPN KSZ9031RNXCA
Y1: Oscillator_SMD_25MHz_KX-7; Oscillator_SMD_Geyer_KX-7-4Pin_3.2x2.5mm; MPN ABM8G-25.000MHZ-18-D2Y-T

Connections:
1V2_SYS: C122.1, C123.1, C124.1, C126.1, C130.1, C135.1, C139.1, C142.1, C145.1, FB2.2, FB3.2, U9.14 (DVDDL), U9.18 (DVDDL), U9.23 (DVDDL), U9.26 (DVDDL), U9.30 (DVDDL), U9.39 (DVDDL)
3V3_SYS: C127.1, C132.1, C137.1, C141.1, C144.1, FB1.1, R58.2, R60.2, R62.2, R63.2, R64.2, R65.2, R66.2, R67.2, R68.2, R69.2, R70.2, R71.2, R72.2, U9.16 (DVDDH), U9.34 (DVDDH), U9.40 (DVDDH)
AVDDH: C128.1, C133.1, C138.1, FB1.2, U9.1 (AVDDH), U9.12 (AVDDH)
AVDDL: C131.1, C136.1, C140.1, C143.1, FB3.1, U9.4 (AVDDL), U9.9 (AVDDL)
AVDDL_PLL: C125.2, C129.2, C134.2, FB2.1, U9.44 (AVDDL_PLL)
ETH1_N: J4.2 (D1-), U9.3 (TXRXM_A)
ETH1_P: J4.1 (D1+), U9.2 (TXRXP_A)
ETH2_N: J4.6 (D2-), U9.6 (TXRXM_B)
ETH2_P: J4.3 (D2+), U9.5 (TXRXP_B)
ETH3_N: J4.5 (D3-), U9.8 (TXRXM_C)
ETH3_P: J4.4 (D3+), U9.7 (TXRXP_C)
ETH4_N: J4.8 (D4-), U9.11 (TXRXM_D)
ETH4_P: J4.7 (D4+), U9.10 (TXRXP_D)
ETH_INT_N: U9.38 (~INT/PME)
ETH_MDC: U9.36 (MDC)
ETH_MDIO: R71.1, U9.37 (MDIO)
ETH_REF_CLK: R68.1, R79.1, U9.41 (CLK125_NDO/LED_MODE)
ETH_RSTN: R72.1, U9.42 (~RESET)
ETH_RXD0: R62.1, R73.1, U9.32 (RXD0/MODE0)
ETH_RXD1: R63.1, R74.1, U9.31 (RXD1/MODE1)
ETH_RXD2: R64.1, R75.1, U9.28 (RXD2/MODE2)
ETH_RXD3: R65.1, R76.1, U9.27 (RXD3/MODE3)
ETH_RX_CLK: R67.1, R78.1, U9.35 (RX_CLK/PHYAD2)
ETH_RX_DV: R66.1, R77.1, U9.33 (RX_DV/CLK125_EN)
ETH_TXD0: U9.19 (TXD0)
ETH_TXD1: U9.20 (TXD1)
ETH_TXD2: U9.21 (TXD2)
ETH_TXD3: U9.22 (TXD3)
ETH_TX_CLK: U9.24 (GTX_CLK)
ETH_TX_EN: U9.25 (TX_EN)
GND: C122.2, C123.2, C124.2, C125.1, C126.2, C127.2, C128.2, C129.1, C130.2, C131.2, C132.2, C133.2, C134.1, C135.2, C136.2, C137.2, C138.2, C139.2, C140.2, C141.2, C142.2, C143.2, C144.2, C145.2, C146.2, C147.2, FB4.2, J4.10 (GND), R59.2, R73.2, R74.2, R75.2, R76.2, R77.2, R78.2, R79.2, R80.2, R81.2, U9.29 (VSS), U9.49 (PAD_GND), Y1.2 (SH), Y1.4 (SH)
LED_LINK: J4.12 (LED1_Y-), R70.1, R81.1, U9.17 (LED1/PHAD0/PME_N1)
LED_SPD: J4.14 (LED2_G-), R69.1, R80.1, U9.15 (LED2/PHYAD1)
unnamed: C146.1, R61.1, U9.45 (XO), Y1.1
unnamed: C147.1, R61.2, U9.46 (XI), Y1.3
unnamed: FB4.1, J4.SH
unnamed: J4.11 (LED1_Y+), R58.1
unnamed: J4.13 (LED2_G+), R60.1
unnamed: R59.1, U9.48 (ISET)

Notes on the sheet:
AVDDH decoupling
PHY
AVDDL_PLL decoupling
AVDDL decoupling
Pull down resistors
DVDDH decoupling
DVDDL decoupling
RJ45 Connector
Pull up resistors
