antmicro/ddr5-tester/fpga-banks-16-34.kicad_sch

## KiCad design fpga-banks-16-34.kicad_sch (2024-02-20)

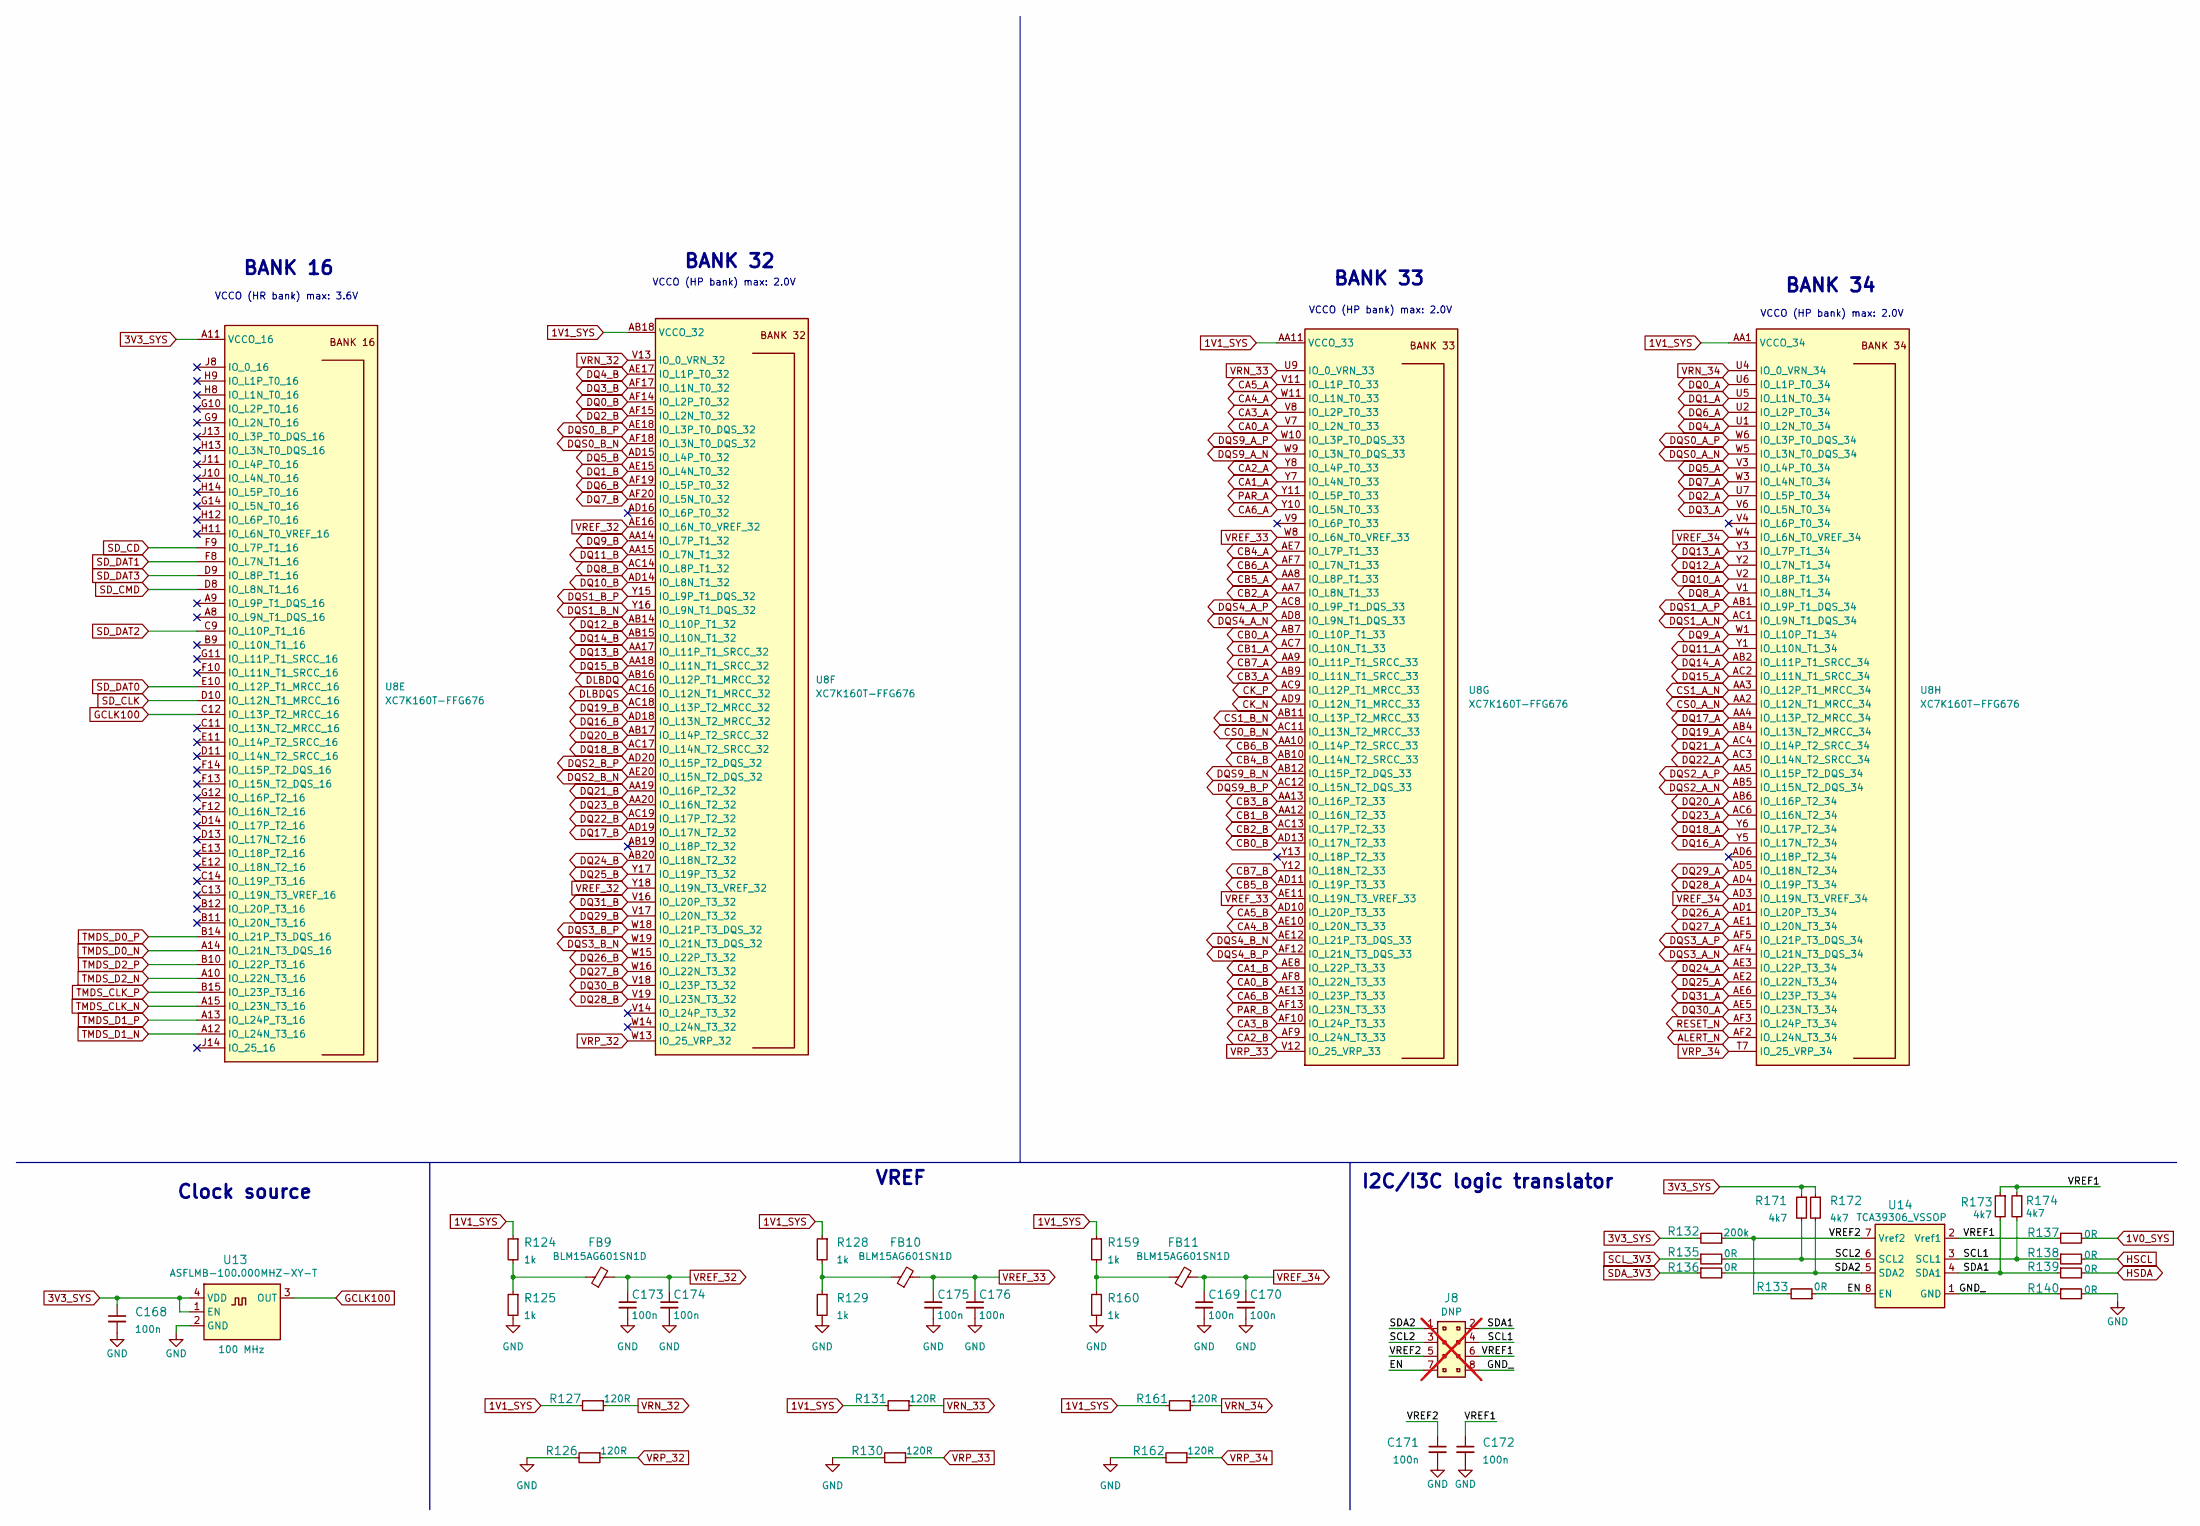
[picture p39: schematic fpga-banks-16-34.kicad_sch]

Parts:
C168, C169, C170, C171, C172, C173, C174, C175, C176: C_100n_6V3_0402; C_0402_1005Metric; MPN 0402X104K6R3CT
FB9, FB10, FB11: FB_600Z_0.3A_0402; FB_0402_1005Metric; MPN BLM15AG601SN1D
J8: PinHeader_2x4_P2.54mm_Drill1mm; PinHeader_2x4_P2.54mm_Drill1.1mm; MPN 62000821121; not fitted
R124, R125, R128, R129, R159, R160: R_1k_0603; R_0603_1608Metric; Tolerance 1%; MPN CR0603-FX-1001ELF
R126, R127, R130, R131, R161, R162: R_120R_0603; R_0603_1608Metric; Tolerance 1%; MPN CR0603-FX-1200ELF
R132: R_200k_0402; R_0402_1005Metric; Tolerance 1%; MPN CR0402-FX-2003GLF
R133, R135, R136, R137, R138, R139, R140: R_0R_0402; R_0402_1005Metric; MPN ERJ2GE0R00X
R171, R172, R173, R174: R_4k7_0402; R_0402_1005Metric; Tolerance 1%; MPN CR0402-FX-4701GLF
U8: XC7K160T-FFG676; BGA-676_27x27mm_Layout26x26_P1X1mm; MPN XC7K160T-FFG676
U13: Oscillator_SMD_100MHz_ASFLMB; Oscillator_SMD_Abracon_ASFLMB_5x3.2x0.85mm; MPN ASFLMB-100.000MHZ-XY-T
U14: TCA39306_VSSOP; VSSOP-8_2.3x2mm_P0.5mm; MPN TCA39306DCUR

Connections:
1V0_SYS: R137.2
1V1_SYS: R124.1, R127.2, R128.1, R131.2, R159.1, R161.2, U8.AA1 (VCCO_34), U8.AA11 (VCCO_33), U8.AB8 (VCCO_33), U8.AB18 (VCCO_32), U8.AC5 (VCCO_34), U8.AC15 (VCCO_32), U8.AD2 (VCCO_34), U8.AD12 (VCCO_33), U8.AE9 (VCCO_33), U8.AE19 (VCCO_32), U8.AF6 (VCCO_34), U8.AF16 (VCCO_32), U8.U3 (VCCO_34), U8.V10 (VCCO_33), U8.W7 (VCCO_33), U8.W17 (VCCO_32), U8.Y4 (VCCO_34), U8.Y14 (VCCO_32)
3V3_SYS: C168.1, R132.2, R171.1, R172.1, U8.A11 (VCCO_16), U8.B8 (VCCO_16), U8.C15 (VCCO_16), U8.D12 (VCCO_16), U8.E9 (VCCO_16), U8.G13 (VCCO_16), U8.H10 (VCCO_16), U13.1 (EN), U13.4 (VDD)
ALERT_N: U8.AF2 (IO_L24N_T3_34)
CA0_A: U8.V7 (IO_L2N_T0_33)
CA0_B: U8.AF8 (IO_L22N_T3_33)
CA1_A: U8.Y7 (IO_L4N_T0_33)
CA1_B: U8.AE8 (IO_L22P_T3_33)
CA2_A: U8.Y8 (IO_L4P_T0_33)
CA2_B: U8.AF9 (IO_L24N_T3_33)
CA3_A: U8.V8 (IO_L2P_T0_33)
CA3_B: U8.AF10 (IO_L24P_T3_33)
CA4_A: U8.W11 (IO_L1N_T0_33)
CA4_B: U8.AE10 (IO_L20N_T3_33)
CA5_A: U8.V11 (IO_L1P_T0_33)
CA5_B: U8.AD10 (IO_L20P_T3_33)
CA6_A: U8.Y10 (IO_L5N_T0_33)
CA6_B: U8.AE13 (IO_L23P_T3_33)
CB0_A: U8.AB7 (IO_L10P_T1_33)
CB0_B: U8.AD13 (IO_L17N_T2_33)
CB1_A: U8.AC7 (IO_L10N_T1_33)
CB1_B: U8.AA12 (IO_L16N_T2_33)
CB2_A: U8.AA7 (IO_L8N_T1_33)
CB2_B: U8.AC13 (IO_L17P_T2_33)
CB3_A: U8.AB9 (IO_L11N_T1_SRCC_33)
CB3_B: U8.AA13 (IO_L16P_T2_33)
CB4_A: U8.AE7 (IO_L7P_T1_33)
CB4_B: U8.AB10 (IO_L14N_T2_SRCC_33)
CB5_A: U8.AA8 (IO_L8P_T1_33)
CB5_B: U8.AD11 (IO_L19P_T3_33)
CB6_A: U8.AF7 (IO_L7N_T1_33)
CB6_B: U8.AA10 (IO_L14P_T2_SRCC_33)
CB7_A: U8.AA9 (IO_L11P_T1_SRCC_33)
CB7_B: U8.Y12 (IO_L18N_T2_33)
CK_N: U8.AD9 (IO_L12N_T1_MRCC_33)
CK_P: U8.AC9 (IO_L12P_T1_MRCC_33)
CS0_A_N: U8.AA2 (IO_L12N_T1_MRCC_34)
CS0_B_N: U8.AC11 (IO_L13N_T2_MRCC_33)
CS1_A_N: U8.AA3 (IO_L12P_T1_MRCC_34)
CS1_B_N: U8.AB11 (IO_L13P_T2_MRCC_33)
DLBDQ: U8.AB16 (IO_L12P_T1_MRCC_32)
DLBDQS: U8.AC16 (IO_L12N_T1_MRCC_32)
DQ0_A: U8.U6 (IO_L1P_T0_34)
DQ0_B: U8.AF14 (IO_L2P_T0_32)
DQ1_A: U8.U5 (IO_L1N_T0_34)
DQ1_B: U8.AE15 (IO_L4N_T0_32)
DQ2_A: U8.U7 (IO_L5P_T0_34)
DQ2_B: U8.AF15 (IO_L2N_T0_32)
DQ3_A: U8.V6 (IO_L5N_T0_34)
DQ3_B: U8.AF17 (IO_L1N_T0_32)
DQ4_A: U8.U1 (IO_L2N_T0_34)
DQ4_B: U8.AE17 (IO_L1P_T0_32)
DQ5_A: U8.V3 (IO_L4P_T0_34)
DQ5_B: U8.AD15 (IO_L4P_T0_32)
DQ6_A: U8.U2 (IO_L2P_T0_34)
DQ6_B: U8.AF19 (IO_L5P_T0_32)
DQ7_A: U8.W3 (IO_L4N_T0_34)
DQ7_B: U8.AF20 (IO_L5N_T0_32)
DQ8_A: U8.V1 (IO_L8N_T1_34)
DQ8_B: U8.AC14 (IO_L8P_T1_32)
DQ9_A: U8.W1 (IO_L10P_T1_34)
DQ9_B: U8.AA14 (IO_L7P_T1_32)
DQ10_A: U8.V2 (IO_L8P_T1_34)
DQ10_B: U8.AD14 (IO_L8N_T1_32)
DQ11_A: U8.Y1 (IO_L10N_T1_34)
DQ11_B: U8.AA15 (IO_L7N_T1_32)
DQ12_A: U8.Y2 (IO_L7N_T1_34)
DQ12_B: U8.AB14 (IO_L10P_T1_32)
DQ13_A: U8.Y3 (IO_L7P_T1_34)
DQ13_B: U8.AA17 (IO_L11P_T1_SRCC_32)
DQ14_A: U8.AB2 (IO_L11P_T1_SRCC_34)
DQ14_B: U8.AB15 (IO_L10N_T1_32)
DQ15_A: U8.AC2 (IO_L11N_T1_SRCC_34)
DQ15_B: U8.AA18 (IO_L11N_T1_SRCC_32)
DQ16_A: U8.Y5 (IO_L17N_T2_34)
DQ16_B: U8.AD18 (IO_L13N_T2_MRCC_32)
DQ17_A: U8.AA4 (IO_L13P_T2_MRCC_34)
DQ17_B: U8.AD19 (IO_L17N_T2_32)
DQ18_A: U8.Y6 (IO_L17P_T2_34)
DQ18_B: U8.AC17 (IO_L14N_T2_SRCC_32)
DQ19_A: U8.AB4 (IO_L13N_T2_MRCC_34)
DQ19_B: U8.AC18 (IO_L13P_T2_MRCC_32)
DQ20_A: U8.AB6 (IO_L16P_T2_34)
DQ20_B: U8.AB17 (IO_L14P_T2_SRCC_32)
DQ21_A: U8.AC4 (IO_L14P_T2_SRCC_34)
DQ21_B: U8.AA19 (IO_L16P_T2_32)
DQ22_A: U8.AC3 (IO_L14N_T2_SRCC_34)
DQ22_B: U8.AC19 (IO_L17P_T2_32)
DQ23_A: U8.AC6 (IO_L16N_T2_34)
DQ23_B: U8.AA20 (IO_L16N_T2_32)
DQ24_A: U8.AE3 (IO_L22P_T3_34)
DQ24_B: U8.AB20 (IO_L18N_T2_32)
DQ25_A: U8.AE2 (IO_L22N_T3_34)
DQ25_B: U8.Y17 (IO_L19P_T3_32)
DQ26_A: U8.AD1 (IO_L20P_T3_34)
DQ26_B: U8.W15 (IO_L22P_T3_32)
DQ27_A: U8.AE1 (IO_L20N_T3_34)
DQ27_B: U8.W16 (IO_L22N_T3_32)
DQ28_A: U8.AD4 (IO_L19P_T3_34)
DQ28_B: U8.V19 (IO_L23N_T3_32)
DQ29_A: U8.AD5 (IO_L18N_T2_34)
DQ29_B: U8.V17 (IO_L20N_T3_32)
DQ30_A: U8.AE5 (IO_L23N_T3_34)
DQ30_B: U8.V18 (IO_L23P_T3_32)
DQ31_A: U8.AE6 (IO_L23P_T3_34)
DQ31_B: U8.V16 (IO_L20P_T3_32)
DQS0_A_N: U8.W5 (IO_L3N_T0_DQS_34)
DQS0_A_P: U8.W6 (IO_L3P_T0_DQS_34)
DQS0_B_N: U8.AF18 (IO_L3N_T0_DQS_32)
DQS0_B_P: U8.AE18 (IO_L3P_T0_DQS_32)
DQS1_A_N: U8.AC1 (IO_L9N_T1_DQS_34)
DQS1_A_P: U8.AB1 (IO_L9P_T1_DQS_34)
DQS1_B_N: U8.Y16 (IO_L9N_T1_DQS_32)
DQS1_B_P: U8.Y15 (IO_L9P_T1_DQS_32)
DQS2_A_N: U8.AB5 (IO_L15N_T2_DQS_34)
DQS2_A_P: U8.AA5 (IO_L15P_T2_DQS_34)
DQS2_B_N: U8.AE20 (IO_L15N_T2_DQS_32)
DQS2_B_P: U8.AD20 (IO_L15P_T2_DQS_32)
DQS3_A_N: U8.AF4 (IO_L21N_T3_DQS_34)
DQS3_A_P: U8.AF5 (IO_L21P_T3_DQS_34)
DQS3_B_N: U8.W19 (IO_L21N_T3_DQS_32)
DQS3_B_P: U8.W18 (IO_L21P_T3_DQS_32)
DQS4_A_N: U8.AD8 (IO_L9N_T1_DQS_33)
DQS4_A_P: U8.AC8 (IO_L9P_T1_DQS_33)
DQS4_B_N: U8.AE12 (IO_L21P_T3_DQS_33)
DQS4_B_P: U8.AF12 (IO_L21N_T3_DQS_33)
DQS9_A_N: U8.W9 (IO_L3N_T0_DQS_33)
DQS9_A_P: U8.W10 (IO_L3P_T0_DQS_33)
DQS9_B_N: U8.AB12 (IO_L15P_T2_DQS_33)
DQS9_B_P: U8.AC12 (IO_L15N_T2_DQS_33)
EN: J8.7, R133.1, U14.8 (EN)
GCLK100: U8.C12 (IO_L13P_T2_MRCC_16), U13.3 (OUT)
GND: C168.2, C169.2, C170.2, C171.2, C172.2, C173.2, C174.2, C175.2, C176.2, R125.2, R126.2, R129.2, R130.2, R140.2, R160.2, R162.2, U13.2 (GND)
GND_: J8.8, R140.1, U14.1 (GND)
HSCL: R138.2
HSDA: R139.2
unnamed: FB9.1, R124.2, R125.1
unnamed: FB10.1, R128.2, R129.1
unnamed: FB11.1, R159.2, R160.1
PAR_A: U8.Y11 (IO_L5P_T0_33)
PAR_B: U8.AF13 (IO_L23N_T3_33)
RESET_N: U8.AF3 (IO_L24P_T3_34)
SCL1: J8.4, R138.1, R174.2, U14.3 (SCL1)
SCL2: J8.3, R135.2, R171.2, U14.6 (SCL2)
SCL_3V3: R135.1
SDA1: J8.2, R139.1, R173.2, U14.4 (SDA1)
SDA2: J8.1, R136.2, R172.2, U14.5 (SDA2)
SDA_3V3: R136.1
SD_CD: U8.F9 (IO_L7P_T1_16)
SD_CLK: U8.D10 (IO_L12N_T1_MRCC_16)
SD_CMD: U8.D8 (IO_L8N_T1_16)
SD_DAT0: U8.E10 (IO_L12P_T1_MRCC_16)
SD_DAT1: U8.F8 (IO_L7N_T1_16)
SD_DAT2: U8.C9 (IO_L10P_T1_16)
SD_DAT3: U8.D9 (IO_L8P_T1_16)
TMDS_CLK_N: U8.A15 (IO_L23N_T3_16)
TMDS_CLK_P: U8.B15 (IO_L23P_T3_16)
TMDS_D0_N: U8.A14 (IO_L21N_T3_DQS_16)
TMDS_D0_P: U8.B14 (IO_L21P_T3_DQS_16)
TMDS_D1_N: U8.A12 (IO_L24N_T3_16)
TMDS_D1_P: U8.A13 (IO_L24P_T3_16)
TMDS_D2_N: U8.A10 (IO_L22N_T3_16)
TMDS_D2_P: U8.B10 (IO_L22P_T3_16)
VREF1: C172.1, J8.6, R137.1, R173.1, R174.1, U14.2 (Vref1)
VREF2: C171.1, J8.5, R132.1, R133.2, U14.7 (Vref2)
VREF_32: C173.1, C174.1, FB9.2, U8.AE16 (IO_L6N_T0_VREF_32), U8.Y18 (IO_L19N_T3_VREF_32)
VREF_33: C175.1, C176.1, FB10.2, U8.AE11 (IO_L19N_T3_VREF_33), U8.W8 (IO_L6N_T0_VREF_33)
VREF_34: C169.1, C170.1, FB11.2, U8.AD3 (IO_L19N_T3_VREF_34), U8.W4 (IO_L6N_T0_VREF_34)
VRN_32: R127.1, U8.V13 (IO_0_VRN_32)
VRN_33: R131.1, U8.U9 (IO_0_VRN_33)
VRN_34: R161.1, U8.U4 (IO_0_VRN_34)
VRP_32: R126.1, U8.W13 (IO_25_VRP_32)
VRP_33: R130.1, U8.V12 (IO_25_VRP_33)
VRP_34: R162.1, U8.T7 (IO_25_VRP_34)

Notes on the sheet:
Clock source
VCCO (HP bank) max: 2.0V
BANK 32
I2C/I3C logic translator
BANK 16
BANK 34
BANK 33
VCCO (HR bank) max: 3.6V
VREF
