antmicro/ddr5-tester/fpga-power.kicad_sch

## KiCad design fpga-power.kicad_sch (2024-02-20)

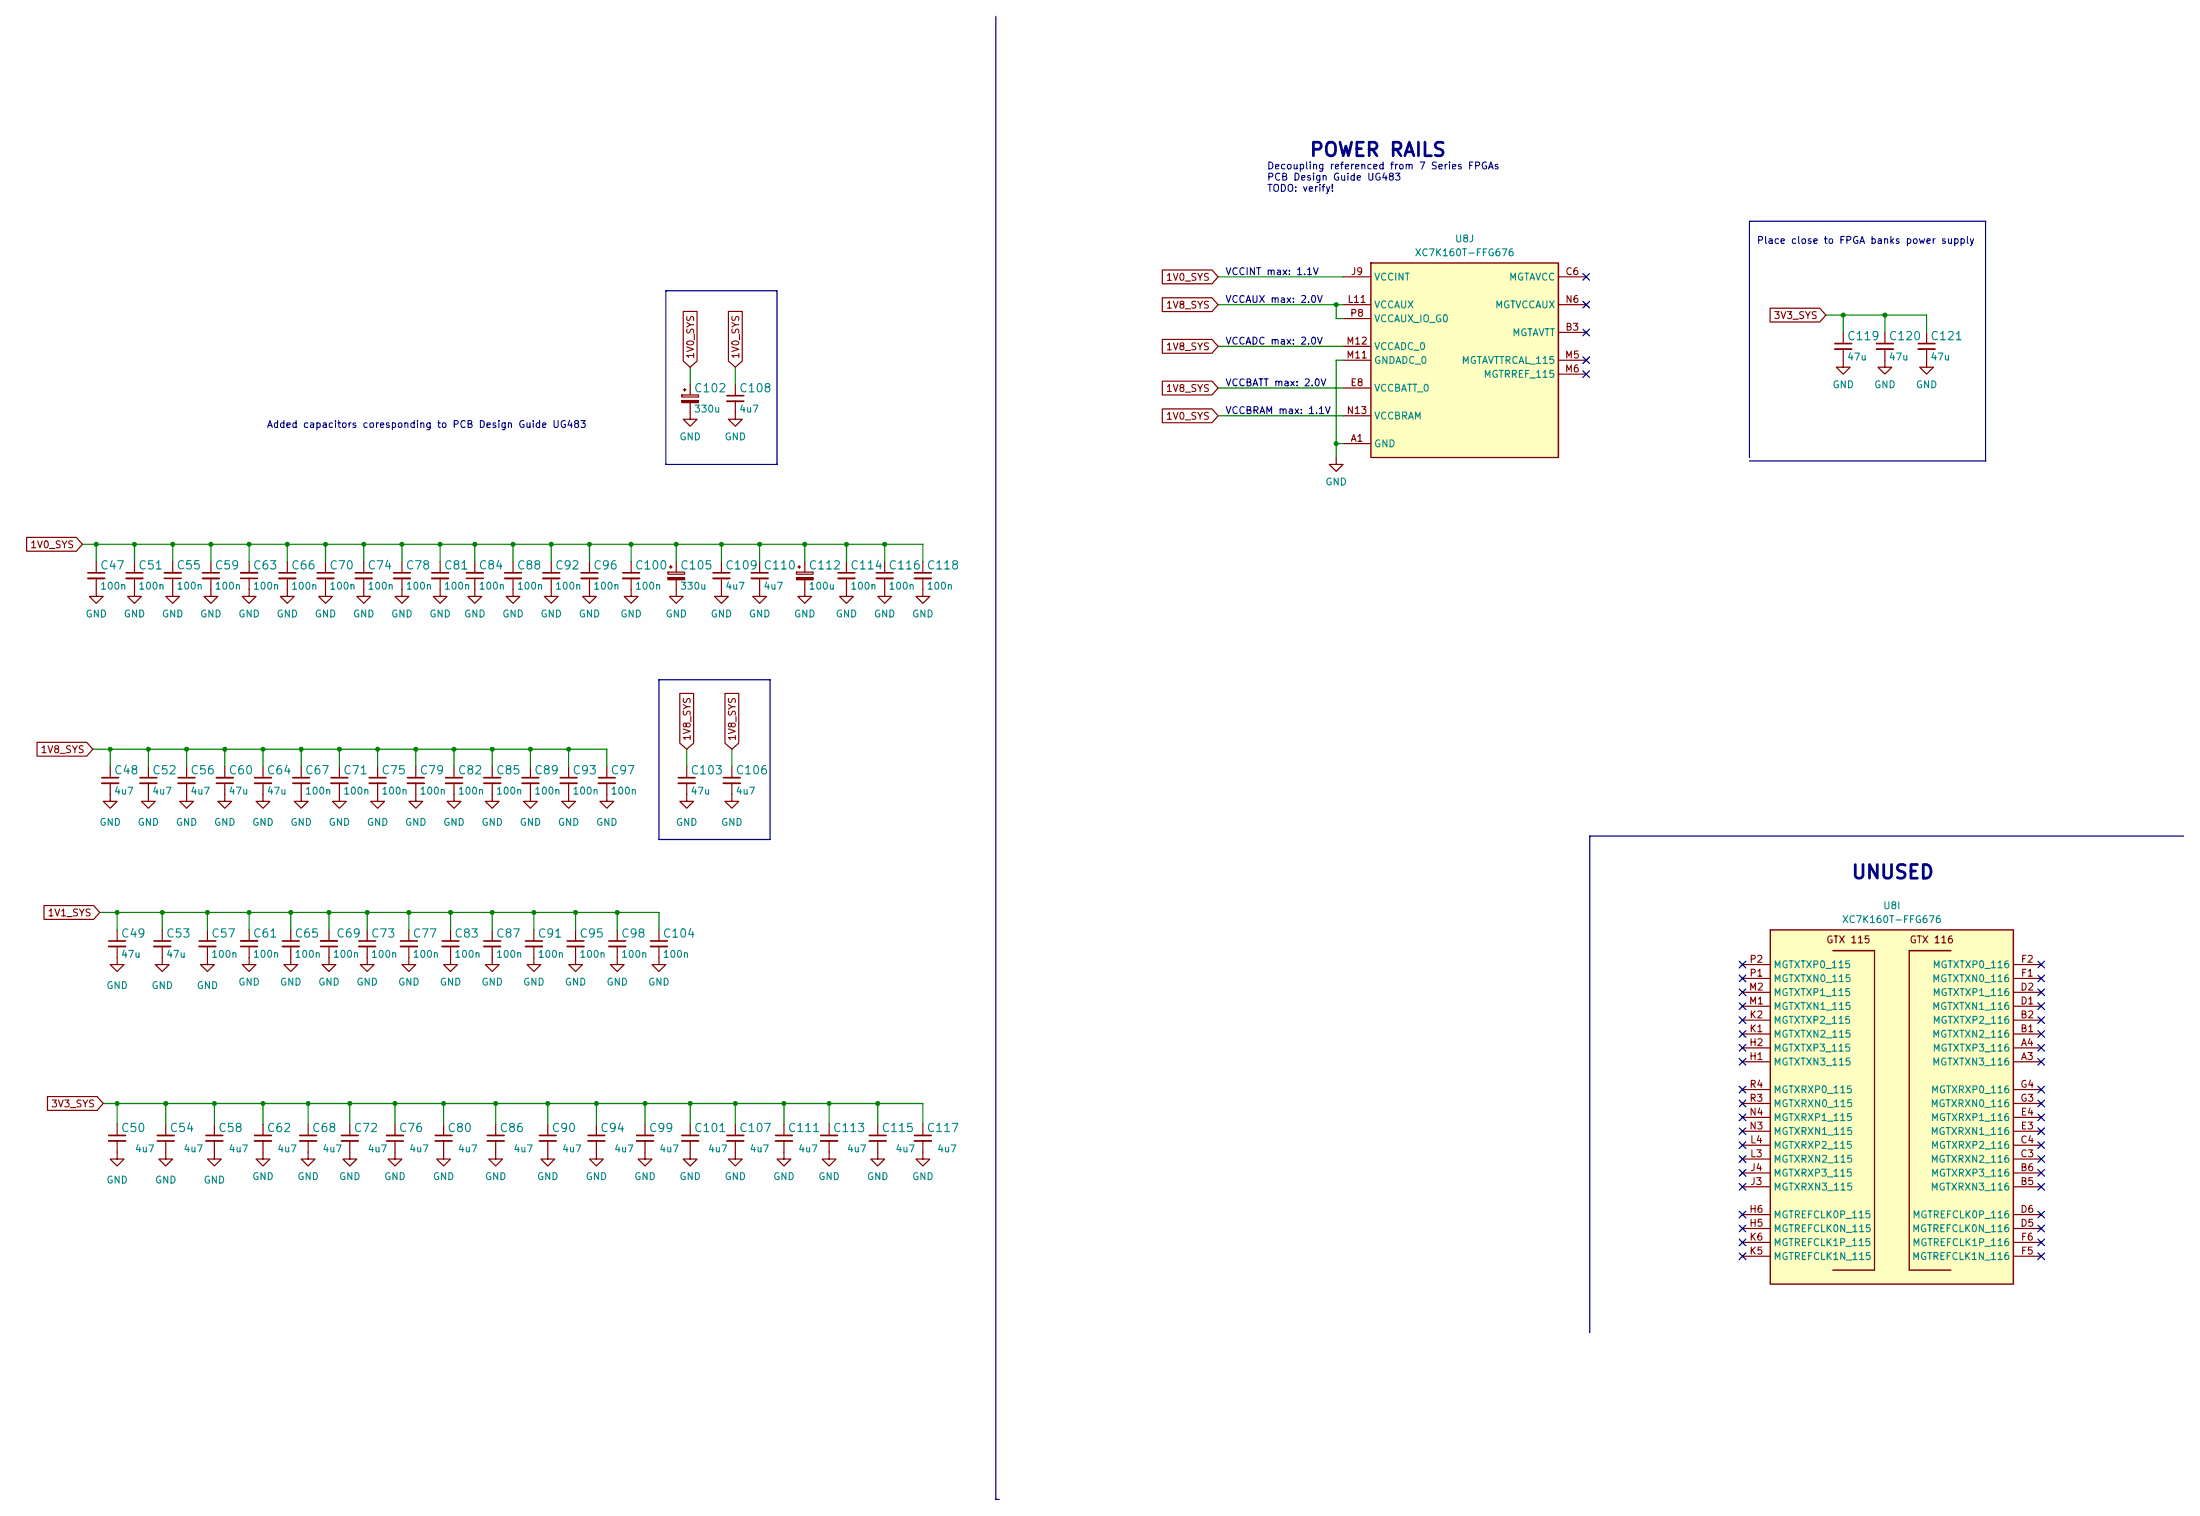
[picture p40: schematic fpga-power.kicad_sch]

Parts:
C47, C51, C55, C57, C59, C61, C63, C65, C66, C67, C69, C70, C71, C73, C74, C75, C77, C78, C79, C81, C82, C83, C84, C85, C87, C88, C89, C91, C92, C93, C95, C96, C97, C98, C100, C104, C114, C116, C118: C_100n_0201; C_0201; MPN CC0201KRX6S5BB104
C48, C50, C52, C54, C56, C58, C62, C68, C72, C76, C80, C86, C90, C94, C99, C101, C106, C107, C108, C109, C110, C111, C113, C115, C117: C_4u7_0402; C_0402_1005Metric; MPN GRM155R61A475MEAAD
C49, C53, C60, C64, C103, C119, C120, C121: C_47u_0603; C_0603_1608Metric; MPN GRM188R60J476ME15D
C102, C105: C_330u_KEMET_D; KEMET_D; MPN T520D337M006ATE045
C112: C_100u_KEMET_A; KEMET_A; MPN 298D107X06R3A2T
U8: XC7K160T-FFG676; BGA-676_27x27mm_Layout26x26_P1X1mm; MPN XC7K160T-FFG676

Connections:
1V0_SYS: C47.1, C51.1, C55.2, C59.1, C63.2, C66.1, C70.1, C74.1, C78.1, C81.1, C84.2, C88.1, C92.1, C96.1, C100.1, C102.1, C105.1, C108.1, C109.1, C110.1, C112.1, C114.1, C116.1, C118.1, U8.J9 (VCCINT), U8.K8 (VCCINT), U8.K10 (VCCINT), U8.K12 (VCCINT), U8.K14 (VCCINT), U8.L9 (VCCINT), U8.L13 (VCCINT), U8.L15 (VCCINT), U8.M8 (VCCINT), U8.M14 (VCCINT), U8.N9 (VCCINT), U8.N13 (VCCBRAM), U8.N15 (VCCINT), U8.P14 (VCCINT), U8.R13 (VCCBRAM), U8.R15 (VCCINT), U8.T12 (VCCBRAM), U8.T14 (VCCINT), U8.U13 (VCCBRAM), U8.U15 (VCCINT)
1V1_SYS: C49.1, C53.1, C57.1, C61.2, C65.1, C69.2, C73.1, C77.1, C83.1, C87.1, C91.1, C95.1, C98.1, C104.1
1V8_SYS: C48.1, C52.1, C56.1, C60.2, C64.1, C67.1, C71.1, C75.1, C79.1, C82.1, C85.1, C89.1, C93.1, C97.1, C103.1, C106.1, U8.E8 (VCCBATT_0), U8.L11 (VCCAUX), U8.M10 (VCCAUX), U8.M12 (VCCADC_0), U8.P8 (VCCAUX_IO_G0), U8.P10 (VCCAUX), U8.R9 (VCCAUX_IO_G0), U8.T8 (VCCAUX_IO_G0), U8.T10 (VCCAUX), U8.U11 (VCCAUX)
3V3_SYS: C50.1, C54.2, C58.1, C62.1, C68.1, C72.1, C76.2, C80.1, C86.1, C90.1, C94.1, C99.1, C101.1, C107.1, C111.1, C113.1, C115.1, C117.1, C119.1, C120.1, C121.1
GND: C47.2, C48.2, C49.2, C50.2, C51.2, C52.2, C53.2, C54.1, C55.1, C56.2, C57.2, C58.2, C59.2, C60.1, C61.1, C62.2, C63.1, C64.2, C65.2, C66.2, C67.2, C68.2, C69.1, C70.2, C71.2, C72.2, C73.2, C74.2, C75.2, C76.1, C77.2, C78.2, C79.2, C80.2, C81.2, C82.2, C83.2, C84.1, C85.2, C86.2, C87.2, C88.2, C89.2, C90.2, C91.2, C92.2, C93.2, C94.2, C95.2, C96.2, C97.2, C98.2, C99.2, C100.2, C101.2, C102.2, C103.2, C104.2, C105.2, C106.2, C107.2, C108.2, C109.2, C110.2, C111.2, C112.2, C113.2, C114.2, C115.2, C116.2, C117.2, C118.2, C119.2, C120.2, C121.2, U8.A1 (GND), U8.A2 (GND), U8.A5 (GND), U8.A6 (GND), U8.A7 (GND), U8.A16 (GND), U8.A26 (GND), U8.AA6 (GND), U8.AA16 (GND), U8.AA26 (GND), U8.AB3 (GND), U8.AB13 (GND), U8.AB23 (GND), U8.AC10 (GND), U8.AC20 (GND), U8.AD7 (GND), U8.AD17 (GND), U8.AE4 (GND), U8.AE14 (GND), U8.AE24 (GND), U8.AF1 (GND), U8.AF11 (GND), U8.AF21 (GND), U8.B4 (GND), U8.B7 (GND), U8.B13 (GND), U8.B23 (GND), U8.C1 (GND), U8.C5 (GND), U8.C7 (GND), U8.C10 (GND), U8.C20 (GND), U8.D4 (GND), U8.D7 (GND), U8.D17 (GND), U8.E1 (GND), U8.E2 (GND), U8.E5 (GND), U8.E7 (GND), U8.E14 (GND), U8.E24 (GND), U8.F3 (GND), U8.F4 (GND), U8.F7 (GND), U8.F11 (GND), U8.F21 (GND), U8.G1 (GND), U8.G5 (GND), U8.G8 (GND), U8.G18 (GND), U8.H4 (GND), U8.H7 (GND), U8.H15 (GND), U8.H25 (GND), U8.J1 (GND), U8.J2 (GND), U8.J5 (GND), U8.J12 (GND), U8.J22 (GND), U8.K3 (GND), U8.K4 (GND), U8.K7 (GND), U8.K9 (GND), U8.K11 (GND), U8.K13 (GND), U8.K19 (GND), U8.L1 (GND), U8.L5 (GND), U8.L10 (GND), U8.L12 (GND), U8.L14 (GND), U8.L16 (GND), U8.L26 (GND), U8.M4 (GND), U8.M7 (GND), U8.M9 (GND), U8.M11 (GNDADC_0), U8.M13 (GND), U8.M15 (GND), U8.M23 (GND), U8.N1 (GND), U8.N2 (GND), U8.N5 (GND), U8.N7 (GND), U8.N10 (GND), U8.N14 (GND), U8.N20 (GND), U8.P3 (GND), U8.P4 (GND), U8.P9 (GND), U8.P13 (GND), U8.P15 (GND), U8.P17 (GND), U8.R1 (GND), U8.R2 (GND), U8.R5 (GND), U8.R8 (GND), U8.R10 (GND), U8.R14 (GND), U8.R24 (GND), U8.T1 (GND), U8.T3 (GND), U8.T4 (GND), U8.T9 (GND), U8.T11 (GND), U8.T13 (GND), U8.T15 (GND), U8.T21 (GND), U8.U8 (GND), U8.U10 (GND), U8.U12 (GND), U8.U14 (GND), U8.U18 (GND), U8.V5 (GND), U8.V15 (GND), U8.V25 (GND), U8.W2 (GND), U8.W12 (GND), U8.W22 (GND), U8.Y9 (GND), U8.Y19 (GND)
unnamed: U8.B3 (MGTAVTT), U8.C2 (MGTAVTT), U8.D3 (MGTAVTT), U8.G2 (MGTAVTT), U8.H3 (MGTAVTT), U8.L2 (MGTAVTT), U8.M3 (MGTAVTT)
unnamed: U8.C6 (MGTAVCC), U8.E6 (MGTAVCC), U8.G6 (MGTAVCC), U8.J6 (MGTAVCC), U8.L6 (MGTAVCC)

Notes on the sheet:
Decoupling referenced from 7 Series FPGAs PCB Design Guide UG483 TODO: verify!
VCCAUX max: 2.0V
VCCINT max: 1.1V
POWER RAILS
Place close to FPGA banks power supply
UNUSED
VCCADC max: 2.0V
Added capacitors coresponding to PCB Design Guide UG483
VCCBRAM max: 1.1V
VCCBATT max: 2.0V
