antmicro/ddr5-tester/hyperram.kicad_sch

## KiCad design hyperram.kicad_sch (2024-02-20)

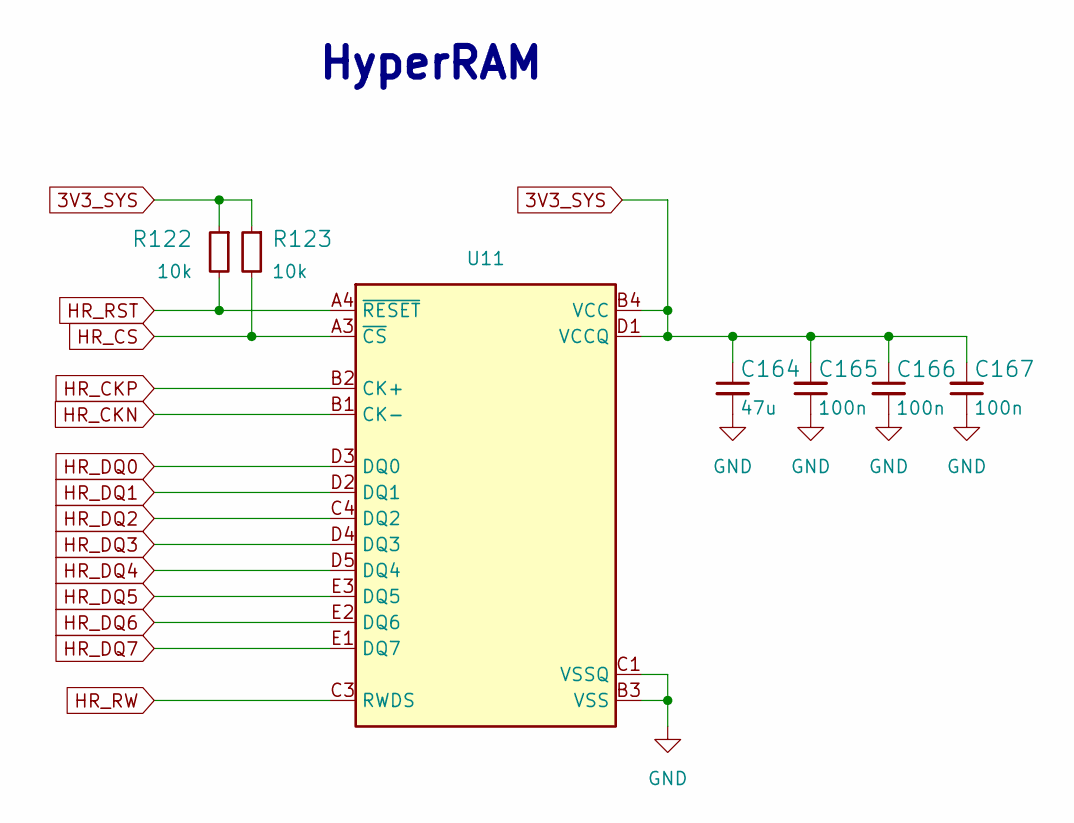
[picture p41: schematic hyperram.kicad_sch]

Parts:
C164: C_47u_0603; C_0603_1608Metric; MPN GRM188R60J476ME15D
C165, C166, C167: C_100n_6V3_0402; C_0402_1005Metric; MPN 0402X104K6R3CT
R122, R123: R_10k_0402; R_0402_1005Metric; Tolerance 1%; MPN CR0402-FX-1002GLF
U11: S27KL0641DABHI023; FBGA-25-24_6x8mm_Layout5x5_P1mm; MPN S27KL0641DABHI023

Connections:
3V3_SYS: C164.1, C165.2, C166.1, C167.2, R122.1, R123.1, U11.B4 (VCC), U11.D1 (VCCQ), U11.E4 (VCCQ)
GND: C164.2, C165.1, C166.2, C167.1, U11.B3 (VSS), U11.C1 (VSSQ), U11.E5 (VSSQ)
HR_CKN: U11.B1 (CK-)
HR_CKP: U11.B2 (CK+)
HR_CS: R123.2, U11.A3 (~CS)
HR_DQ0: U11.D3 (DQ0)
HR_DQ1: U11.D2 (DQ1)
HR_DQ2: U11.C4 (DQ2)
HR_DQ3: U11.D4 (DQ3)
HR_DQ4: U11.D5 (DQ4)
HR_DQ5: U11.E3 (DQ5)
HR_DQ6: U11.E2 (DQ6)
HR_DQ7: U11.E1 (DQ7)
HR_RST: R122.2, U11.A4 (~RESET)
HR_RW: U11.C3 (RWDS)
unnamed: U11.A2 (NC), U11.A5 (NC), U11.B5 (NC), U11.C2 (NC), U11.C5 (NC)

Notes on the sheet:
HyperRAM
