antmicro/ddr5-tester/interfaces.kicad_sch

## KiCad design interfaces.kicad_sch (2024-02-20)

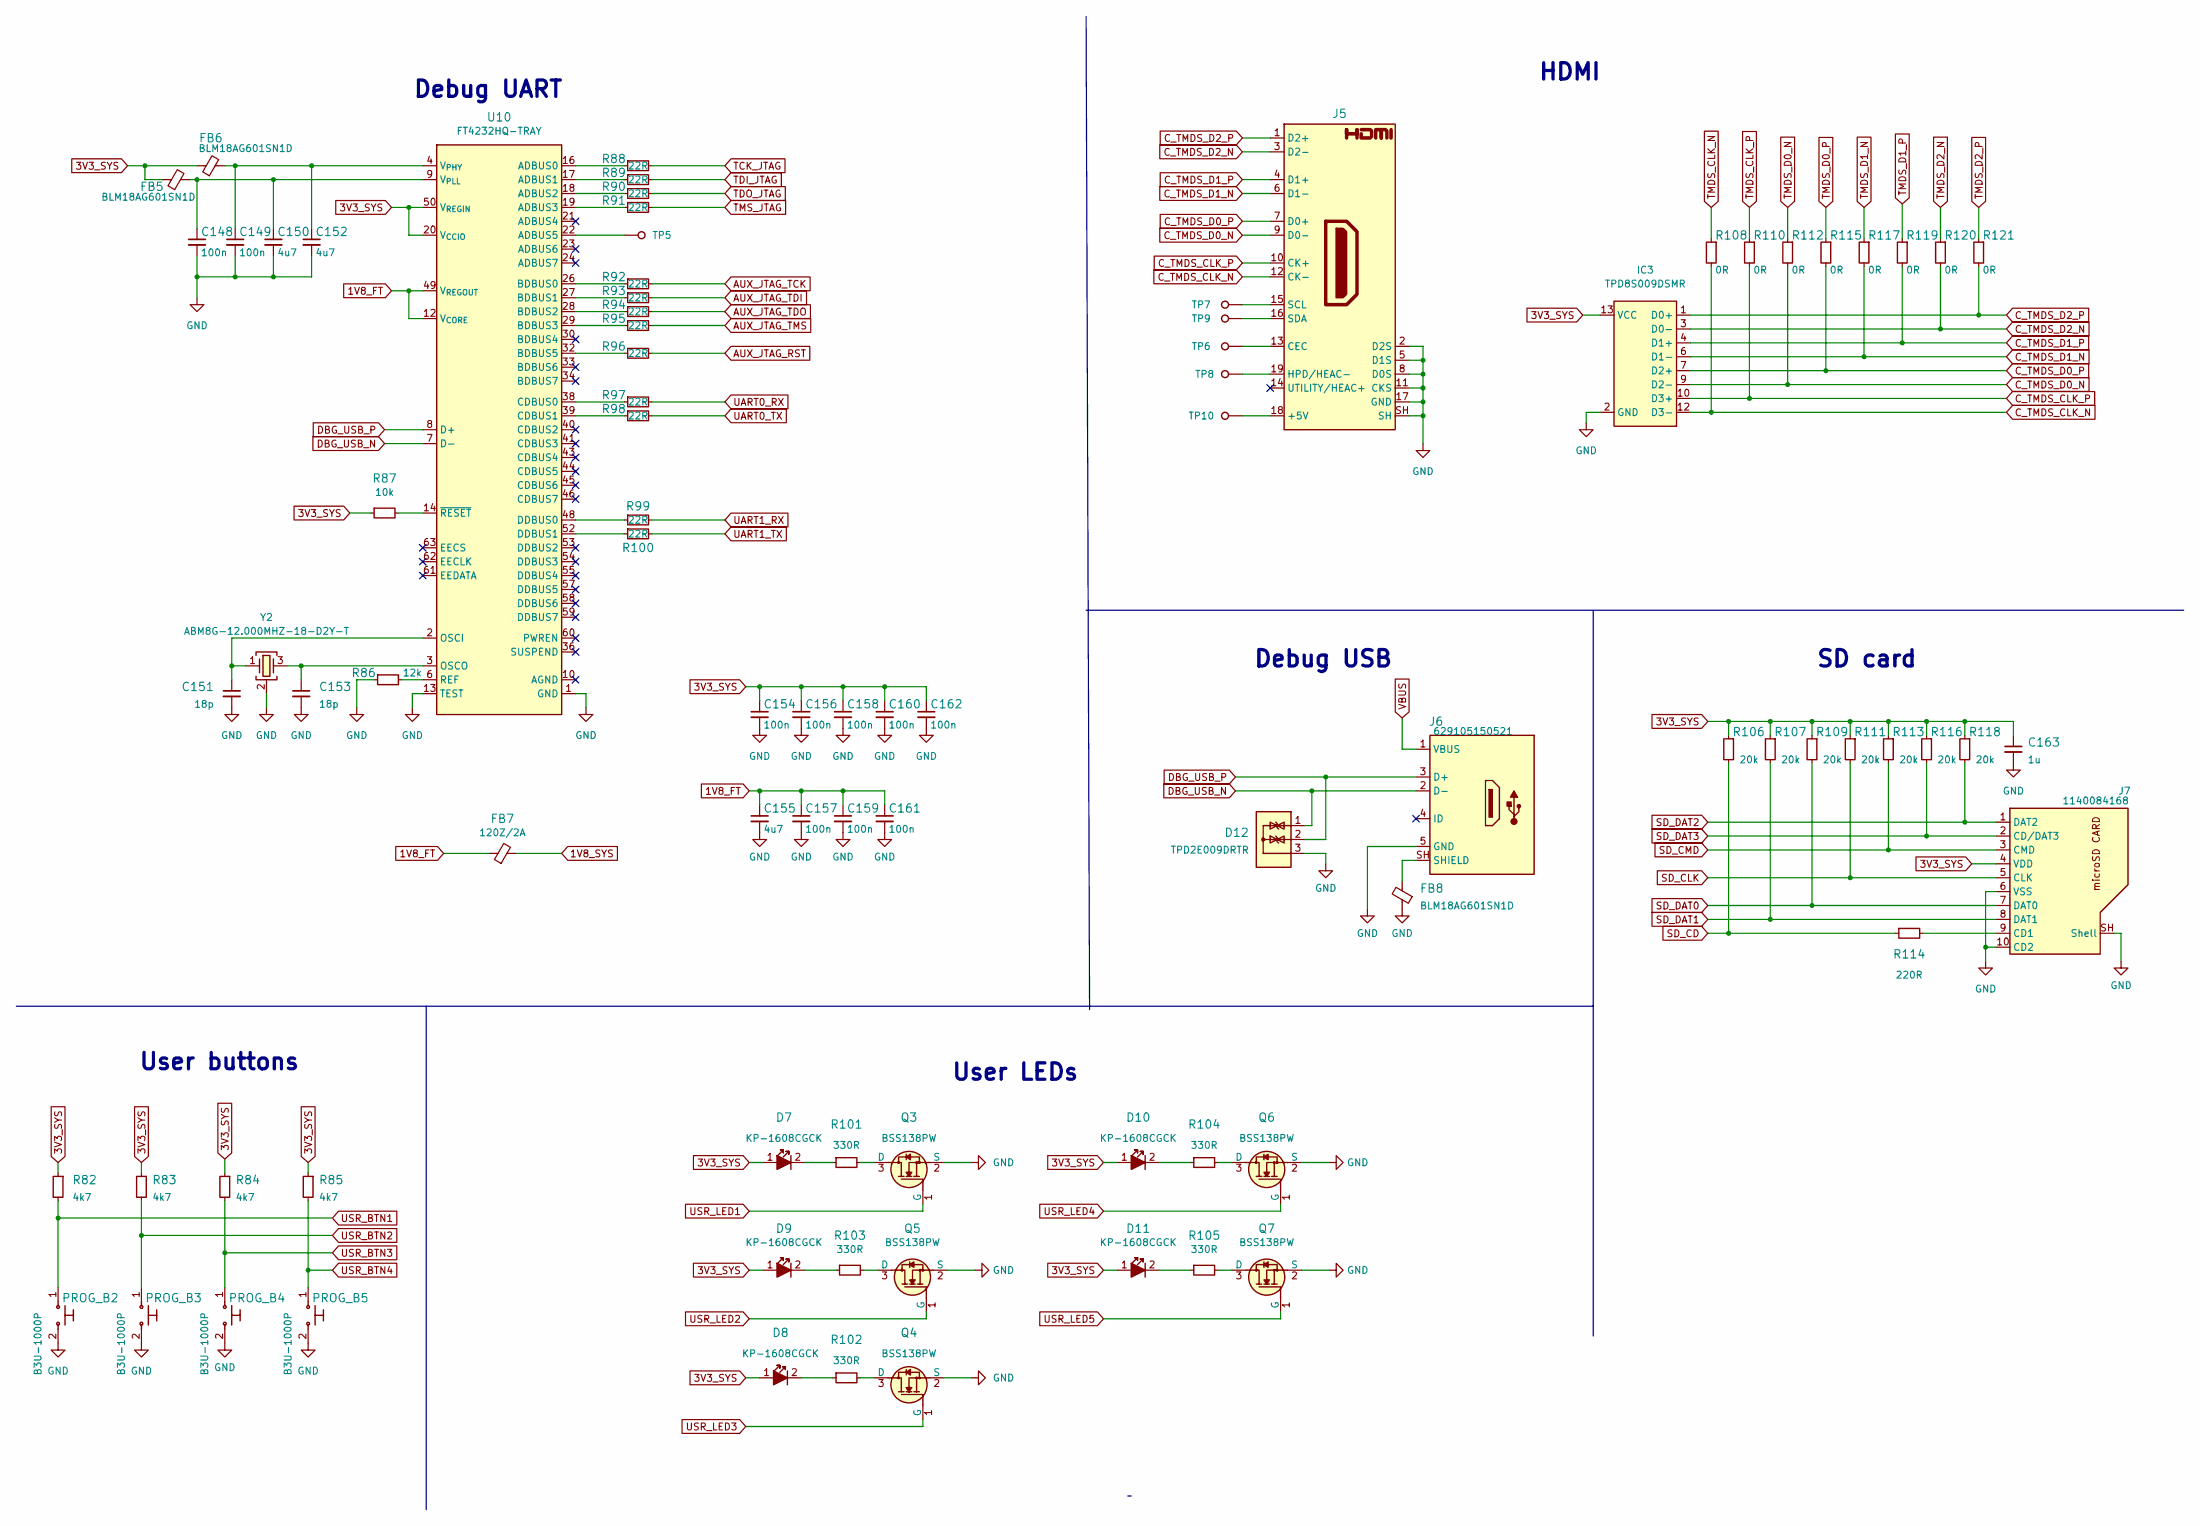
[picture p42: schematic interfaces.kicad_sch]

Parts:
C148, C149, C154, C156, C157, C158, C159, C160, C161, C162: C_100n_6V3_0402; C_0402_1005Metric; MPN 0402X104K6R3CT
C150, C152, C155: C_4u7_0402; C_0402_1005Metric; MPN GRM155R61A475MEAAD
C151, C153: C_18p_0402; C_0402_1005Metric; MPN MC0402N180J500CT
C163: C_1u_0603; C_0603_1608Metric; MPN 0603YD105KAT2A
D7, D8, D9, D10, D11: LED_G_0603_KP-1608CGCK; LED_0603_1608Metric_G; MPN KP-1608CGCK
D12: TPD2E009_SOT-9X3; SOT-723; MPN TPD2E009DRTR
FB5, FB6, FB8: FB_600Z_0.5A_0603; FB_0603_1608Metric; MPN BLM18AG601SN1D
FB7: FB_120Z_2A_0603; FB_0603_1608Metric; MPN BLM18PG121SN1D
IC3: TPD8S009DSMR; R-PDSO-N15; MPN TPD8S009DSMR
J5: HDMI-A_685119134923; HDMI-A_Receptacle_WE_685119134923; MPN 685119134923
J6: USB_Micro-B_629105150521; USB-Micro-B_Receptacle_WE_629105150521; MPN 629105150521
J7: MicroSD_1140084168; MicroSD_Amphenol_1140084168; MPN 1140084168
PROG_B2, PROG_B3, PROG_B4, PROG_B5: SW_B3U-1000P; SW_B3U-1000P_SMD; MPN B3U-1000P
Q3, Q4, Q5, Q6, Q7: BSS138PW; SC70-3; MPN BSS138PW
R82, R83, R84, R85: R_4k7_0402; R_0402_1005Metric; Tolerance 1%; MPN CR0402-FX-4701GLF
R86: R_12k_0402; R_0402_1005Metric; Tolerance 1%; MPN CR0402-FX-1202GLF
R87: R_10k_0402; R_0402_1005Metric; Tolerance 1%; MPN CR0402-FX-1002GLF
R88, R89, R90, R91, R92, R93, R94, R95, R96, R97, R98, R99, R100: R_22R_0402; R_0402_1005Metric; Tolerance 1%; MPN CR0402-FX-22R0GLF
R101, R102, R103, R104, R105: R_330R_0402; R_0402_1005Metric; Tolerance 1%; MPN CR0402-FX-3300GLF
R106, R107, R109, R111, R113, R116, R118: R_20k_0402; R_0402_1005Metric; Tolerance 1%; MPN CR0402-FX-2002GLF
R108, R110, R112, R115, R117, R119, R120, R121: R_0R_0402; R_0402_1005Metric; MPN ERJ2GE0R00X
R114: R_220R_0402; R_0402_1005Metric; Tolerance 1%; MPN CR0402-FX-2200GLF
TP5, TP6, TP7, TP8, TP9, TP10: TP_1mm_SMD; TP_SMD_1mm
U10: FT4232H_QFN; QFN-64-1EP_9x9mm_P0.5mm; MPN FT4232HQ-TRAY
Y2: Oscillator_SMD_12MHz_KX-7; Oscillator_SMD_Geyer_KX-7-4Pin_3.2x2.5mm; MPN ABM8G-12.000MHZ-18-D2Y-T

Connections:
1V8_FT: C155.1, C157.1, C159.1, C161.1, FB7.1, U10.12 (V_{CORE}), U10.37 (V_{CORE}), U10.49 (V_{REGOUT}), U10.64 (V_{CORE})
1V8_SYS: FB7.2
3V3_SYS: C154.1, C156.1, C158.1, C160.1, C162.1, C163.1, D7.1, D8.1, D9.1, D10.1, D11.1, FB5.1, FB6.1, IC3.13 (VCC), IC3.15 (VCC), J7.4 (VDD), R82.1, R83.1, R84.1, R85.1, R87.1, R106.1, R107.1, R109.1, R111.1, R113.1, R116.1, R118.1, U10.20 (V_{CCIO}), U10.31 (V_{CCIO}), U10.42 (V_{CCIO}), U10.50 (V_{REGIN}), U10.56 (V_{CCIO})
AUX_JTAG_RST: R96.2
AUX_JTAG_TCK: R92.2
AUX_JTAG_TDI: R93.2
AUX_JTAG_TDO: R94.2
AUX_JTAG_TMS: R95.2
C_TMDS_CLK_N: IC3.12 (D3-), J5.12 (CK-), R108.2
C_TMDS_CLK_P: IC3.10 (D3+), J5.10 (CK+), R110.2
C_TMDS_D0_N: IC3.9 (D2-), J5.9 (D0-), R112.2
C_TMDS_D0_P: IC3.7 (D2+), J5.7 (D0+), R115.2
C_TMDS_D1_N: IC3.6 (D1-), J5.6 (D1-), R117.2
C_TMDS_D1_P: IC3.4 (D1+), J5.4 (D1+), R119.2
C_TMDS_D2_N: IC3.3 (D0-), J5.3 (D2-), R120.2
C_TMDS_D2_P: IC3.1 (D0+), J5.1 (D2+), R121.2
DBG_USB_N: D12.1, J6.2 (D-), U10.7 (D-)
DBG_USB_P: D12.2, J6.3 (D+), U10.8 (D+)
GND: C148.2, C149.2, C150.2, C151.2, C152.2, C153.2, C154.2, C155.2, C156.2, C157.2, C158.2, C159.2, C160.2, C161.2, C162.2, C163.2, D12.3, FB8.1, IC3.2 (GND), IC3.5 (GND), IC3.8 (GND), IC3.11 (GND), J5.2 (D2S), J5.5 (D1S), J5.8 (D0S), J5.11 (CKS), J5.17 (GND), J5.SH, J6.5 (GND), J7.6 (VSS), J7.10 (CD2), J7.SH (Shell), PROG_B2.2, PROG_B3.2, PROG_B4.2, PROG_B5.2, Q3.2 (S), Q4.2 (S), Q5.2 (S), Q6.2 (S), Q7.2 (S), R86.1, U10.1 (GND), U10.5 (GND), U10.11 (GND), U10.13 (TEST), U10.15 (GND), U10.25 (GND), U10.35 (GND), U10.47 (GND), U10.51 (GND), U10.65 (GND), Y2.2 (SH), Y2.4 (SH)
unnamed: C148.1, C150.1, FB5.2, U10.9 (V_{PLL})
unnamed: C149.1, C152.1, FB6.2, U10.4 (V_{PHY})
unnamed: C151.1, U10.2 (OSCI), Y2.1
unnamed: C153.1, U10.3 (OSCO), Y2.3
unnamed: D7.2, R101.1
unnamed: D8.2, R102.1
unnamed: D9.2, R103.1
unnamed: D10.2, R104.1
unnamed: D11.2, R105.1
unnamed: FB8.2, J6.SH (SHIELD)
unnamed: J5.13 (CEC), TP6.1
unnamed: J5.15 (SCL), TP7.1
unnamed: J5.16 (SDA), TP9.1
unnamed: J5.18 (+5V), TP10.1
unnamed: J5.19 (HPD/HEAC-), TP8.1
unnamed: J7.9 (CD1), R114.2
unnamed: Q3.3 (D), R101.2
unnamed: Q4.3 (D), R102.2
unnamed: Q5.3 (D), R103.2
unnamed: Q6.3 (D), R104.2
unnamed: Q7.3 (D), R105.2
unnamed: R86.2, U10.6 (REF)
unnamed: R87.2, U10.14 (~RESET)
unnamed: R88.1, U10.16 (ADBUS0)
unnamed: R89.1, U10.17 (ADBUS1)
unnamed: R90.1, U10.18 (ADBUS2)
unnamed: R91.1, U10.19 (ADBUS3)
unnamed: R92.1, U10.26 (BDBUS0)
unnamed: R93.1, U10.27 (BDBUS1)
unnamed: R94.1, U10.28 (BDBUS2)
unnamed: R95.1, U10.29 (BDBUS3)
unnamed: R96.1, U10.32 (BDBUS5)
unnamed: R97.1, U10.38 (CDBUS0)
unnamed: R98.1, U10.39 (CDBUS1)
unnamed: R99.1, U10.48 (DDBUS0)
unnamed: R100.1, U10.52 (DDBUS1)
unnamed: TP5.1, U10.22 (ADBUS5)
SD_CD: R106.2, R114.1
SD_CLK: J7.5 (CLK), R111.2
SD_CMD: J7.3 (CMD), R113.2
SD_DAT0: J7.7 (DAT0), R109.2
SD_DAT1: J7.8 (DAT1), R107.2
SD_DAT2: J7.1 (DAT2), R118.2
SD_DAT3: J7.2 (CD/DAT3), R116.2
TCK_JTAG: R88.2
TDI_JTAG: R89.2
TDO_JTAG: R90.2
TMDS_CLK_N: R108.1
TMDS_CLK_P: R110.1
TMDS_D0_N: R112.1
TMDS_D0_P: R115.1
TMDS_D1_N: R117.1
TMDS_D1_P: R119.1
TMDS_D2_N: R120.1
TMDS_D2_P: R121.1
TMS_JTAG: R91.2
UART0_RX: R97.2
UART0_TX: R98.2
UART1_RX: R99.2
UART1_TX: R100.2
USR_BTN1: PROG_B2.1, R82.2
USR_BTN2: PROG_B3.1, R83.2
USR_BTN3: PROG_B4.1, R84.2
USR_BTN4: PROG_B5.1, R85.2
USR_LED1: Q3.1 (G)
USR_LED2: Q5.1 (G)
USR_LED3: Q4.1 (G)
USR_LED4: Q6.1 (G)
USR_LED5: Q7.1 (G)
VBUS: J6.1 (VBUS)

Notes on the sheet:
Debug USB
SD card
User LEDs
HDMI
User buttons
Debug UART
