antmicro/ddr5-tester/supply.kicad_sch

## KiCad design supply.kicad_sch (2024-02-20)

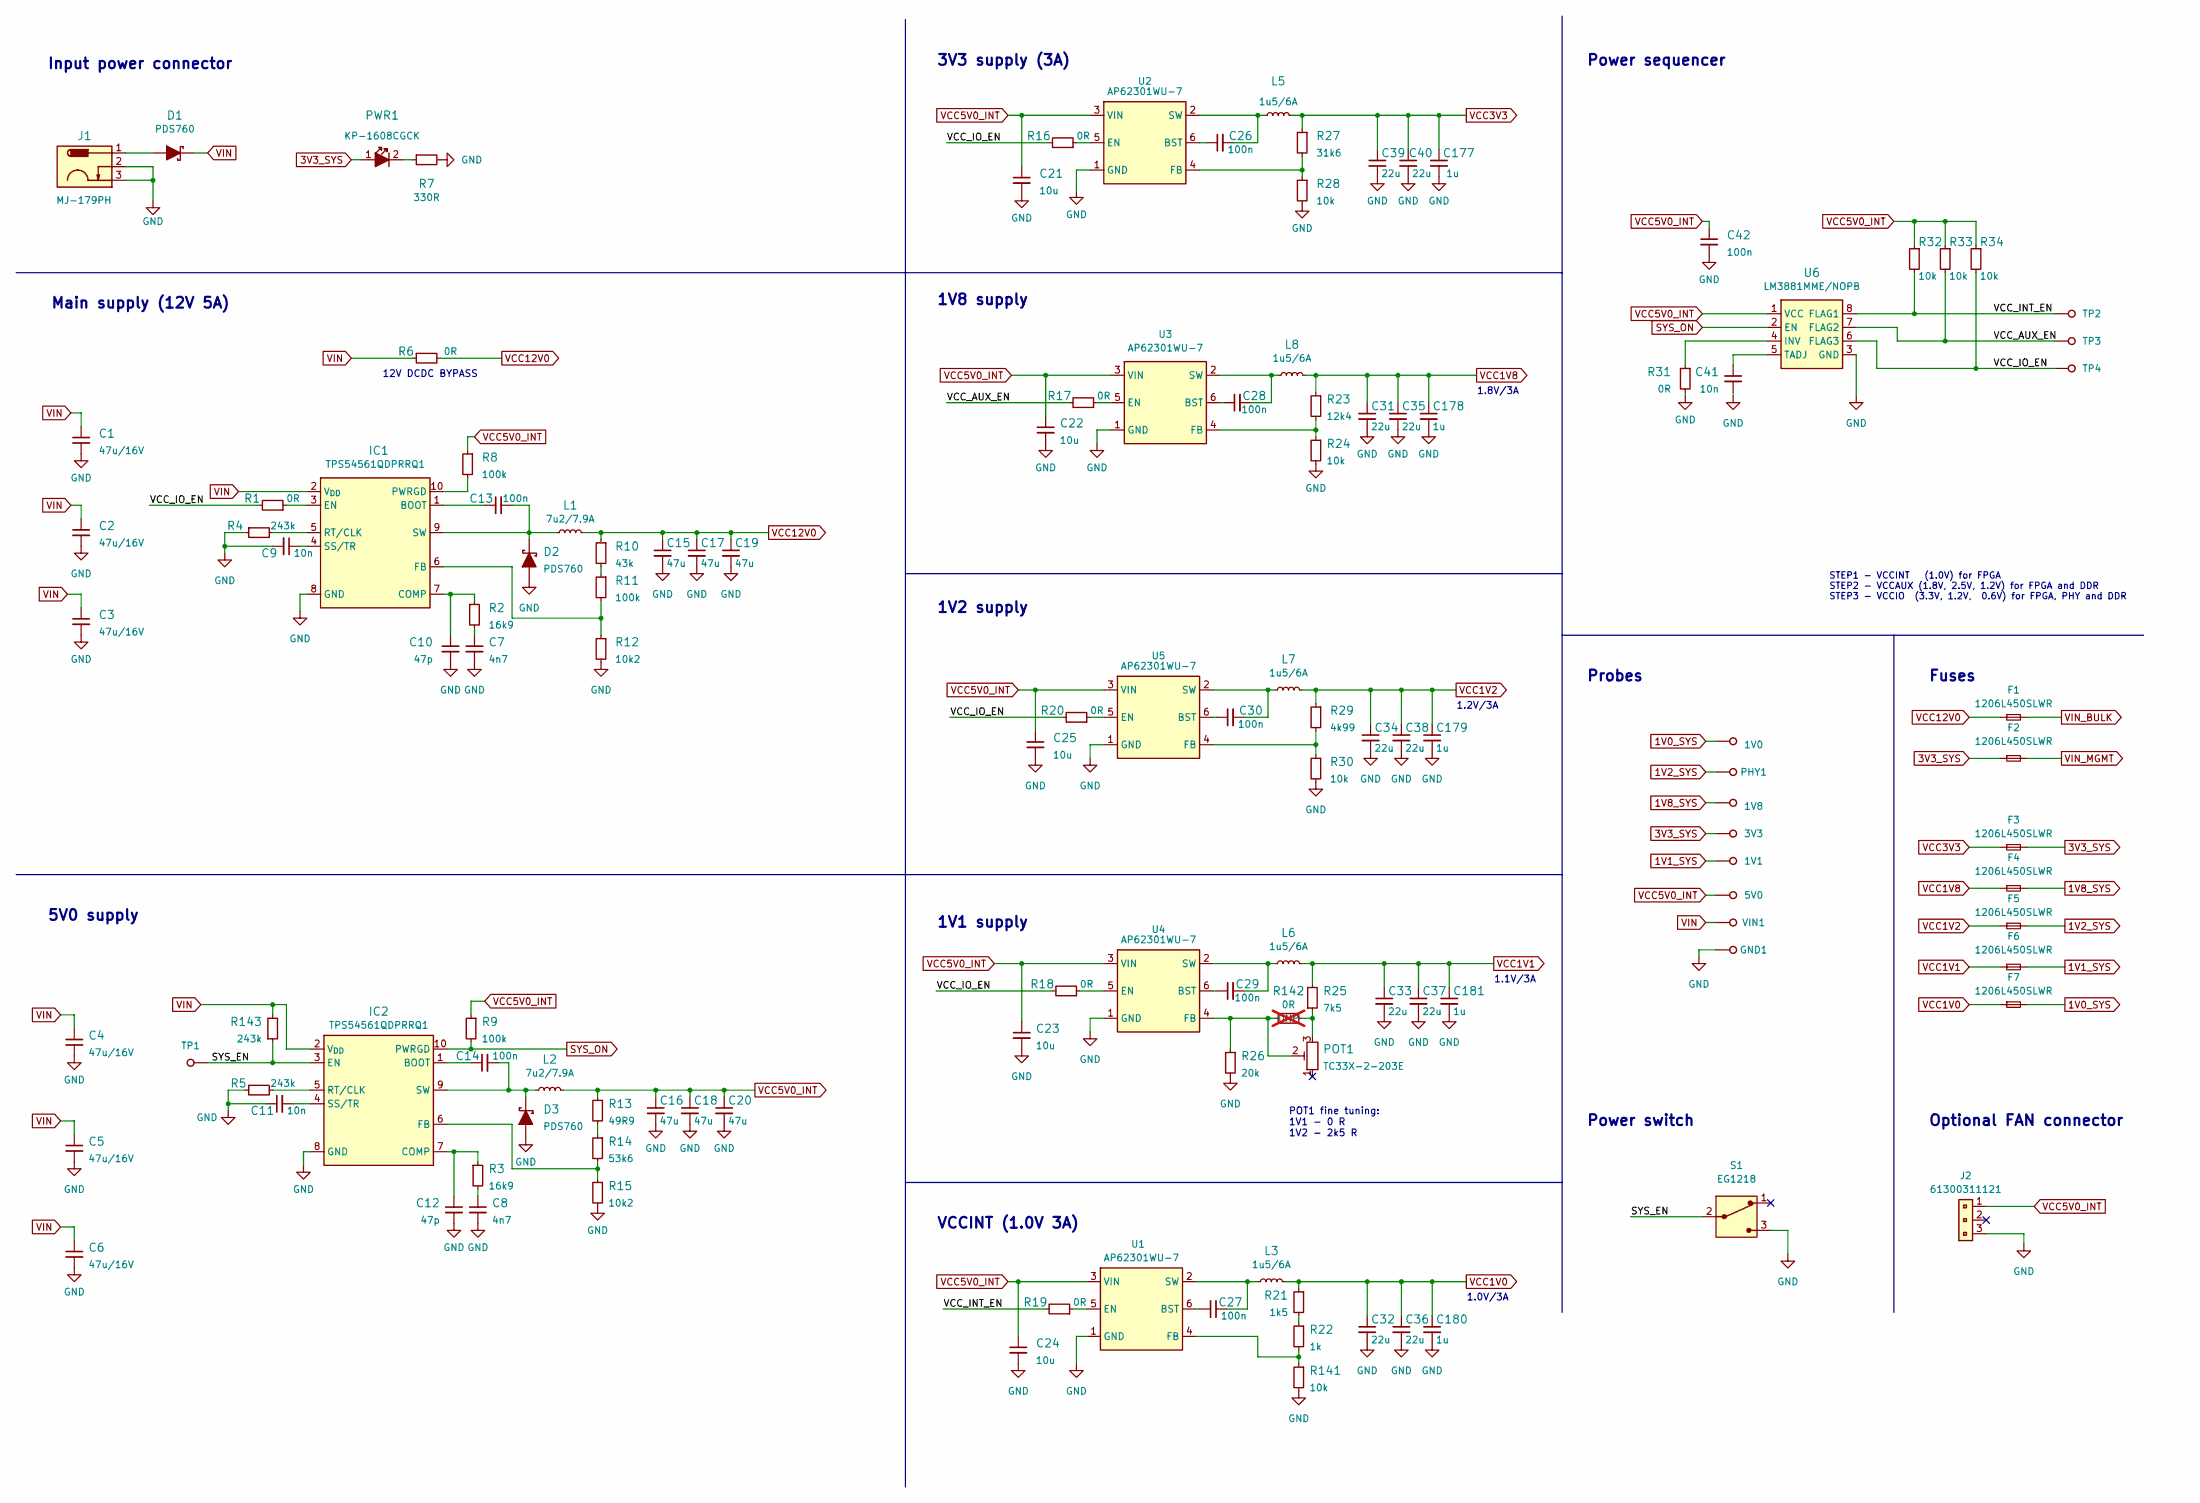
[picture p43: schematic supply.kicad_sch]

Parts:
1V0, 1V1, 1V8, 3V3, 5V0: TP_1mm_SMD; TP_SMD_1mm
C1, C2, C3, C4, C5, C6: C_47u_16V_1206; C_1206_3216Metric; MPN C3216X5R1C476M160AB
C7, C8: C_4n7_0402; C_0402_1005Metric; MPN CGA2B3X7S2A472K050BB
C9, C11: C_10n_0402; C_0402_1005Metric; Voltage 50V; MPN GRM155R71H103KA88D
C10, C12: C_47p_0402; C_0402_1005Metric; MPN GRM1555C1E470JA01D
C13, C14, C26, C27, C28, C29, C30, C42: C_100n_6V3_0402; C_0402_1005Metric; MPN 0402X104K6R3CT
C15, C16, C17, C18, C19, C20: C_47u_0603; C_0603_1608Metric; MPN GRM188R60J476ME15D
C21, C22, C23, C24, C25: C_10u_0402; C_0402_1005Metric; MPN CC0402MRX5R5BB106
C31, C32, C33, C34, C35, C36, C37, C38, C39, C40: C_22u_0402; C_0402_1005Metric; MPN 04024W226MAT2A
C41: C_10n_0603; C_0603_1608Metric; MPN 06031C103JAT2A
C177, C178, C179, C180, C181: C_1u_0402; C_0402_1005Metric; MPN C1005X6S1A105K050BC
D1, D2, D3: PDS760; PowerDI5; MPN PDS760-13
F1, F2, F3, F4, F5, F6, F7: PTC_4.5A_1206; F_1206_3216Metric; MPN 1206L450SLWR
GND1: TP_1mm_SMD; TP_SMD_1mm
IC1, IC2: TPS54561QDPRRQ1; WSON-10-1EP_4x4mm_P0.8mm_EP2.6x3mm; MPN TPS54561QDPRRQ1
J1: BarrelJack_3167288; BarrelJack_3167288_Horizontal; MPN MJ-179PH
J2: PinHeader_1x3_P2.54mm_Drill1.1mm; MPN 61300311121
L1, L2: L_7u2_7.9A_WE-PDF; L_WE-PDF; MPN 7447798720
L3, L5, L6, L7, L8: L_1u5_6A_1716; L_1716_4441Metric; MPN SRP0420-1R5K
PHY1: TP_1mm_SMD; TP_SMD_1mm
POT1: TC33X-2-203E; Trimpot_3.8mmx3.6mm_TC33X-2-103E; MPN TC33X-2-203E
PWR1: LED_G_0603_KP-1608CGCK; LED_0603_1608Metric_G; MPN KP-1608CGCK
R1, R16, R17, R18, R19, R20, R31: R_0R_0402; R_0402_1005Metric; MPN ERJ2GE0R00X
R2, R3: R_16k9_0402; R_0402_1005Metric; Tolerance 1%; MPN CR0402-FX-1692GLF
R4, R5, R143: R_243k_0402; R_0402_1005Metric; Tolerance 1%; MPN CR0402-FX-2433GLF
R6: R_0R_2010; R_2010_5025Metric; MPN CRCW20100000Z0EF
R7: R_330R_0402; R_0402_1005Metric; Tolerance 1%; MPN CR0402-FX-3300GLF
R8, R9, R11: R_100k_0402; R_0402_1005Metric; Tolerance 1%; MPN CR0402-FX-1003GLF
R10: R_43k_0402; R_0402_1005Metric; Tolerance 1%; MPN CR0402-FX-4302GLF
R12, R15: R_10k2_0402; R_0402_1005Metric; Tolerance 1%; MPN CR0402-FX-1022GLF
R13: R_49R9_0402; R_0402_1005Metric; Tolerance 1%; MPN CR0402-FX-49R9GLF
R14: R_53k6_0402; R_0402_1005Metric; Tolerance 1%; MPN CR0402-FX-5362GLF
R21: R_1k5_0402; R_0402_1005Metric; Tolerance 1%; MPN CR0402-FX-1501GLF
R22: R_1k_0402; R_0402_1005Metric; Tolerance 1%; MPN CR0402-FX-1001GLF
R23: R_12k4_0402; R_0402_1005Metric; Tolerance 1%; MPN CR0402-FX-1242GLF
R24, R28, R30, R32, R33, R34, R141: R_10k_0402; R_0402_1005Metric; Tolerance 1%; MPN CR0402-FX-1002GLF
R25: R_7k5_0402; R_0402_1005Metric; Tolerance 1%; MPN CR0402-FX-7501GLF
R26: R_20k_0402; R_0402_1005Metric; Tolerance 1%; MPN CR0402-FX-2002GLF
R27: R_31k6_0402; R_0402_1005Metric; Tolerance 1%; MPN CR0402-FX-3162GLF
R29: R_4k99_0402; R_0402_1005Metric; Tolerance 1%; MPN CR0402-FX-4991GLF
R142: R_0R_0402; R_0402_1005Metric; MPN ERJ2GE0R00X; not fitted
S1: SW_EG1218; SW_Slide_E-Switch_EG1218; MPN EG1218
TP1, TP2, TP3, TP4: TP_1mm_SMD; TP_SMD_1mm
U1, U2, U3, U4, U5: AP62301WU-7; TSOT23-6; MPN AP62301WU-7
U6: LM3881MME_NOPB; VSSOP-8_3x3mm_P0.65mm; MPN LM3881MME/NOPB
VIN1: TP_1mm_SMD; TP_SMD_1mm

Connections:
1V0_SYS: 1V0.1, F7.2
1V1_SYS: 1V1.1, F6.2
1V2_SYS: F5.2, PHY1.1
1V8_SYS: 1V8.1, F4.2
3V3_SYS: 3V3.1, F2.1, F3.2, PWR1.1
GND: C1.2, C2.2, C3.2, C4.2, C5.2, C6.2, C7.2, C8.2, C9.2, C10.2, C11.1, C12.2, C15.2, C16.2, C17.2, C18.2, C19.2, C20.2, C21.2, C22.2, C23.2, C24.2, C25.2, C31.2, C32.2, C33.2, C34.2, C35.2, C36.2, C37.2, C38.2, C39.2, C40.2, C41.2, C42.2, C177.2, C178.2, C179.2, C180.2, C181.2, D2.A, D3.A, GND1.1, IC1.8 (GND), IC1.11 (GND), IC2.8 (GND), IC2.11 (GND), J1.2, J1.3, J2.3, R4.1, R5.1, R7.2, R12.2, R15.2, R24.2, R26.2, R28.2, R30.2, R31.2, R141.2, S1.3, U1.1 (GND), U2.1 (GND), U3.1 (GND), U4.1 (GND), U5.1 (GND), U6.3 (GND)
unnamed: C7.1, R2.2
unnamed: C8.1, R3.2
unnamed: C9.1, IC1.4 (SS/TR)
unnamed: C10.1, IC1.7 (COMP), R2.1
unnamed: C11.2, IC2.4 (SS/TR)
unnamed: C12.1, IC2.7 (COMP), R3.1
unnamed: C13.1, IC1.1 (BOOT)
unnamed: C13.2, D2.C, IC1.9 (SW), L1.1
unnamed: C14.1, IC2.1 (BOOT)
unnamed: C14.2, D3.C, IC2.9 (SW), L2.1
unnamed: C26.1, U2.6 (BST)
unnamed: C26.2, L5.1, U2.2 (SW)
unnamed: C27.1, U1.6 (BST)
unnamed: C27.2, L3.1, U1.2 (SW)
unnamed: C28.1, U3.6 (BST)
unnamed: C28.2, L8.1, U3.2 (SW)
unnamed: C29.1, U4.6 (BST)
unnamed: C29.2, L6.1, U4.2 (SW)
unnamed: C30.1, U5.6 (BST)
unnamed: C30.2, L7.1, U5.2 (SW)
unnamed: C41.1, U6.5 (TADJ)
unnamed: D1.A, J1.1
unnamed: IC1.3 (EN), R1.1
unnamed: IC1.5 (RT/CLK), R4.2
unnamed: IC1.6 (FB), R11.2, R12.1
unnamed: IC1.10 (PWRGD), R8.2
unnamed: IC2.5 (RT/CLK), R5.2
unnamed: IC2.6 (FB), R14.2, R15.1
unnamed: POT1.2, R26.1, R142.2, U4.4 (FB)
unnamed: POT1.3, R25.1, R142.1
unnamed: PWR1.2, R7.1
unnamed: R10.2, R11.1
unnamed: R13.2, R14.1
unnamed: R16.1, U2.5 (EN)
unnamed: R17.1, U3.5 (EN)
unnamed: R18.1, U4.5 (EN)
unnamed: R19.1, U1.5 (EN)
unnamed: R20.1, U5.5 (EN)
unnamed: R21.2, R22.1
unnamed: R23.2, R24.1, U3.4 (FB)
unnamed: R27.2, R28.1, U2.4 (FB)
unnamed: R29.2, R30.1, U5.4 (FB)
unnamed: R31.1, U6.4 (INV)
unnamed: R22.2, R141.1, U1.4 (FB)
SYS_EN: IC2.3 (EN), R143.1, S1.2, TP1.1
SYS_ON: IC2.10 (PWRGD), R9.2, U6.2 (EN)
VCC1V0: C32.1, C36.1, C180.1, F7.1, L3.2, R21.1
VCC1V1: C33.1, C37.1, C181.1, F6.1, L6.2, R25.2
VCC1V2: C34.1, C38.1, C179.1, F5.1, L7.2, R29.1
VCC1V8: C31.1, C35.1, C178.1, F4.1, L8.2, R23.1
VCC3V3: C39.1, C40.1, C177.1, F3.1, L5.2, R27.1
VCC5V0_INT: 5V0.1, C16.1, C18.1, C20.1, C21.1, C22.1, C23.1, C24.1, C25.1, C42.1, J2.1, L2.2, R8.1, R9.1, R13.1, R32.1, R33.1, R34.1, U1.3 (VIN), U2.3 (VIN), U3.3 (VIN), U4.3 (VIN), U5.3 (VIN), U6.1 (VCC)
VCC12V0: C15.1, C17.1, C19.1, F1.1, L1.2, R6.2, R10.1
VCC_AUX_EN: R17.2, R33.2, TP3.1, U6.7 (FLAG2)
VCC_INT_EN: R19.2, R32.2, TP2.1, U6.8 (FLAG1)
VCC_IO_EN: R1.2, R16.2, R18.2, R20.2, R34.2, TP4.1, U6.6 (FLAG3)
VIN: C1.1, C2.1, C3.1, C4.1, C5.1, C6.1, D1.C, IC1.2 (V_{DD}), IC2.2 (V_{DD}), R6.1, R143.2, VIN1.1
VIN_BULK: F1.2
VIN_MGMT: F2.2

Notes on the sheet:
12V DCDC BYPASS
1V2 supply
Power switch
VCCINT (1.0V 3A)
POT1 fine tuning: 1V1 - 0 R 1V2 - 2k5 R
1.1V/3A
3V3 supply (3A)
Fuses
Probes
1V1 supply
STEP1 - VCCINT (1.0V) for FPGA STEP2 - VCCAUX (1.8V, 2.5V, 1.2V) for FPGA and DDR STEP3 - VCCIO (3.3V, 1.2V, 0.6V) for FPGA, PHY and DDR
5V0 supply
1.2V/3A
Power sequencer
1V8 supply
Optional FAN connector
1.8V/3A
Main supply (12V 5A)
1.0V/3A
Input power connector
